Nickdev8/LedScreen/daftpunkfiles/gloves/images/2013-06-19_19.33.11.jpg

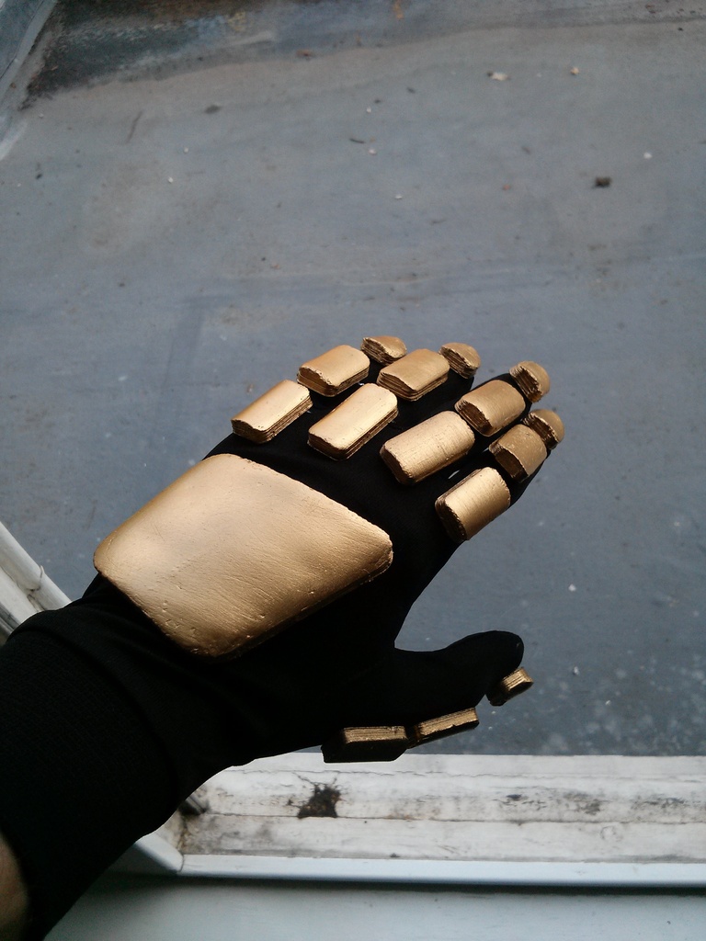
daftpunkfiles/gloves/images/2013-06-19_19.33.11.jpg
