Nickdev8/LedScreen/daftpunkfiles/thomas/p1/images/DisplayLowerBracket-v1.3.jpg

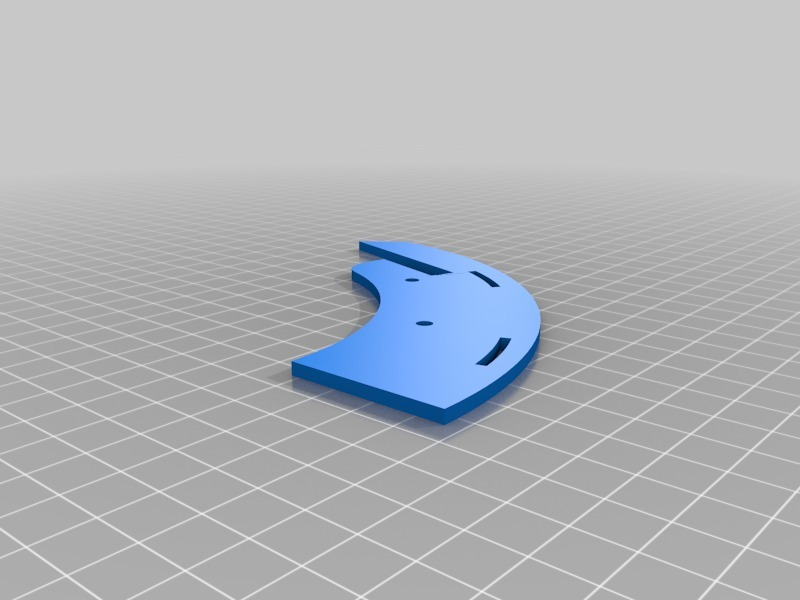
daftpunkfiles/thomas/p1/images/DisplayLowerBracket-v1.3.jpg
