Nickdev8/LedScreen/daftpunkfiles/thomas/p1/images/DisplayupperBracket-v1.3.jpg

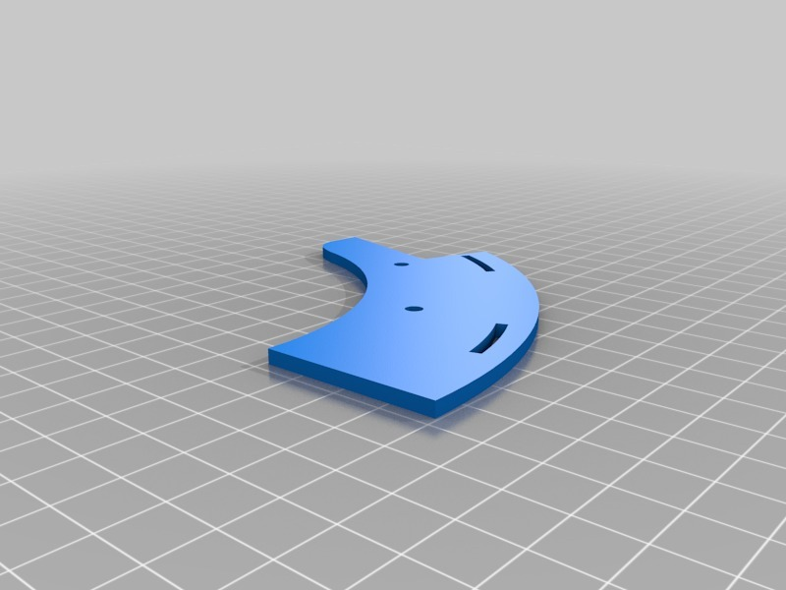
daftpunkfiles/thomas/p1/images/DisplayupperBracket-v1.3.jpg
