Nickdev8/LedScreen/daftpunkfiles/thomas/p1/images/IMG_20140508_220246.jpg

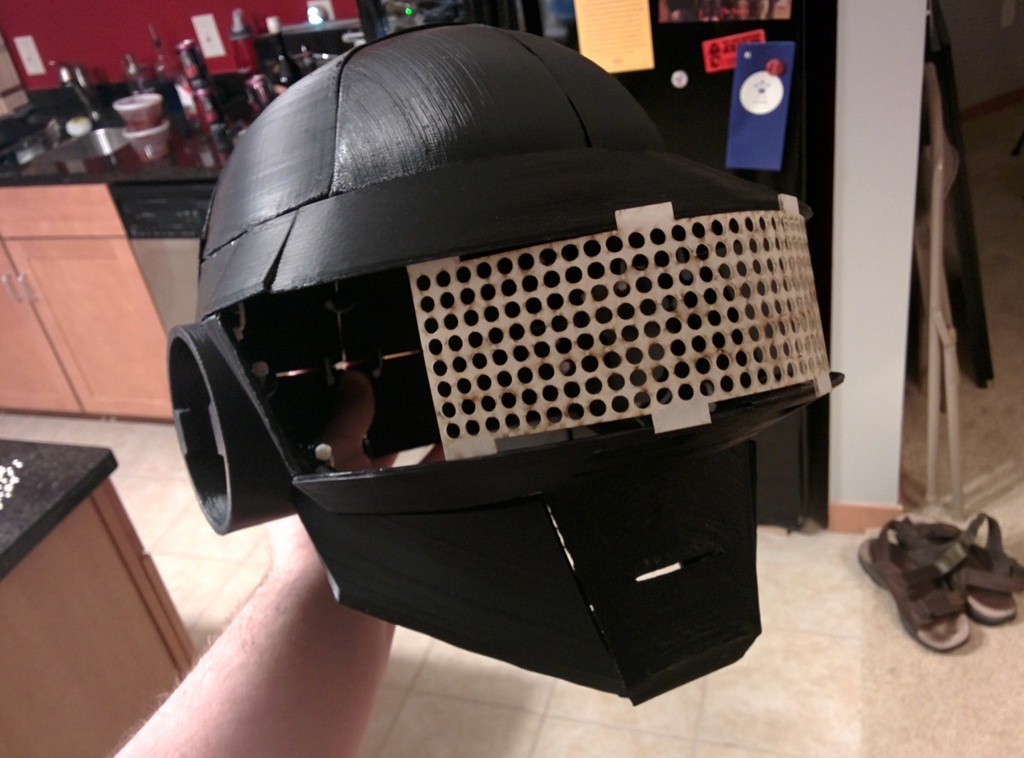
daftpunkfiles/thomas/p1/images/IMG_20140508_220246.jpg
