Nickdev8/LedScreen/daftpunkfiles/thomas/p1/images/June_10__2014_at_1221AM.jpg

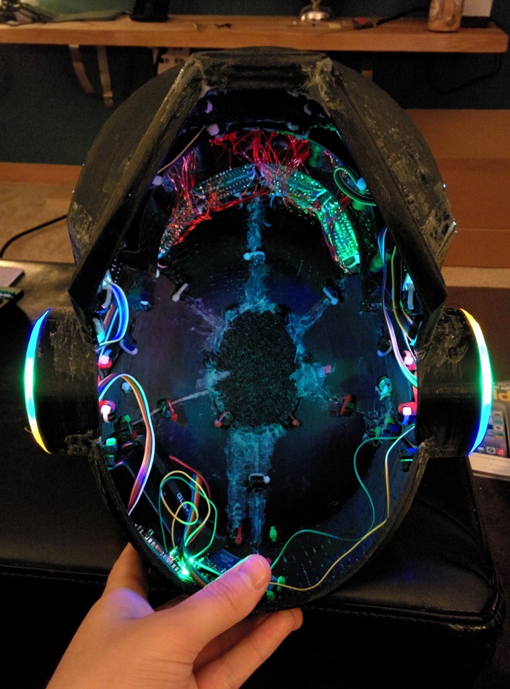
daftpunkfiles/thomas/p1/images/June_10__2014_at_1221AM.jpg
