Nickdev8/LedScreen/daftpunkfiles/thomas/p1/images/LightRing-v1.0.jpg

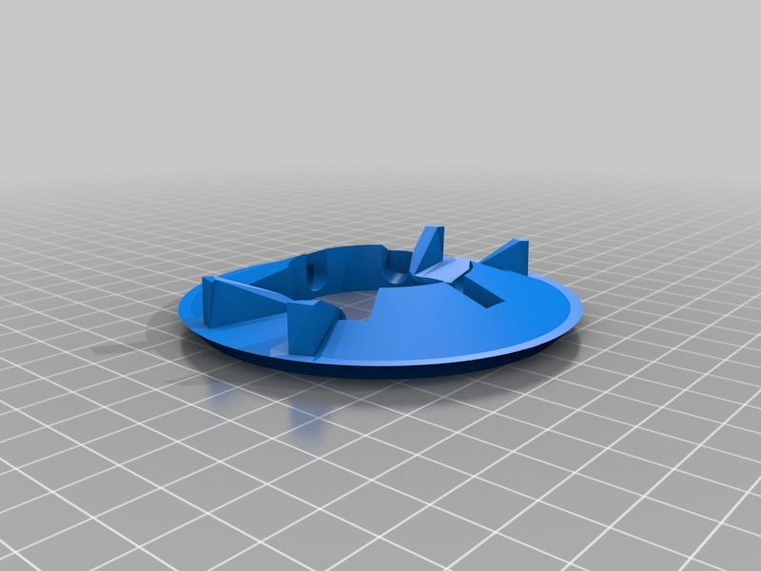
daftpunkfiles/thomas/p1/images/LightRing-v1.0.jpg
