Nickdev8/LedScreen/daftpunkfiles/thomas/p1/images/May_25__2014_at_0116AM.jpg

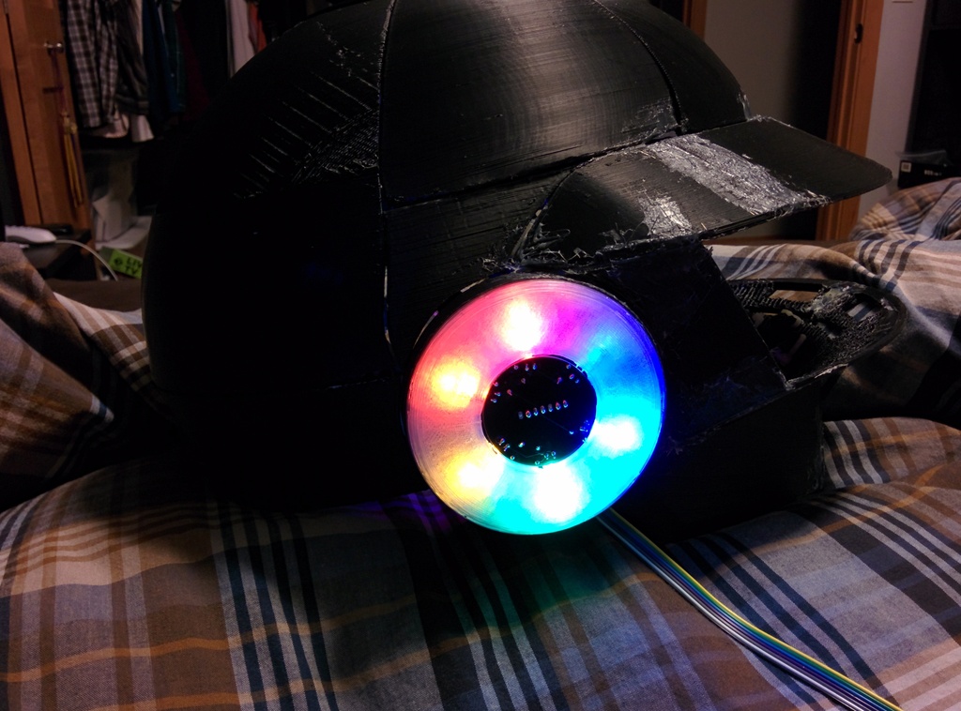
daftpunkfiles/thomas/p1/images/May_25__2014_at_0116AM.jpg
