Nickdev8/LedScreen/daftpunkfiles/thomas/p1/images/November_02__2014_at_0414PM.jpeg

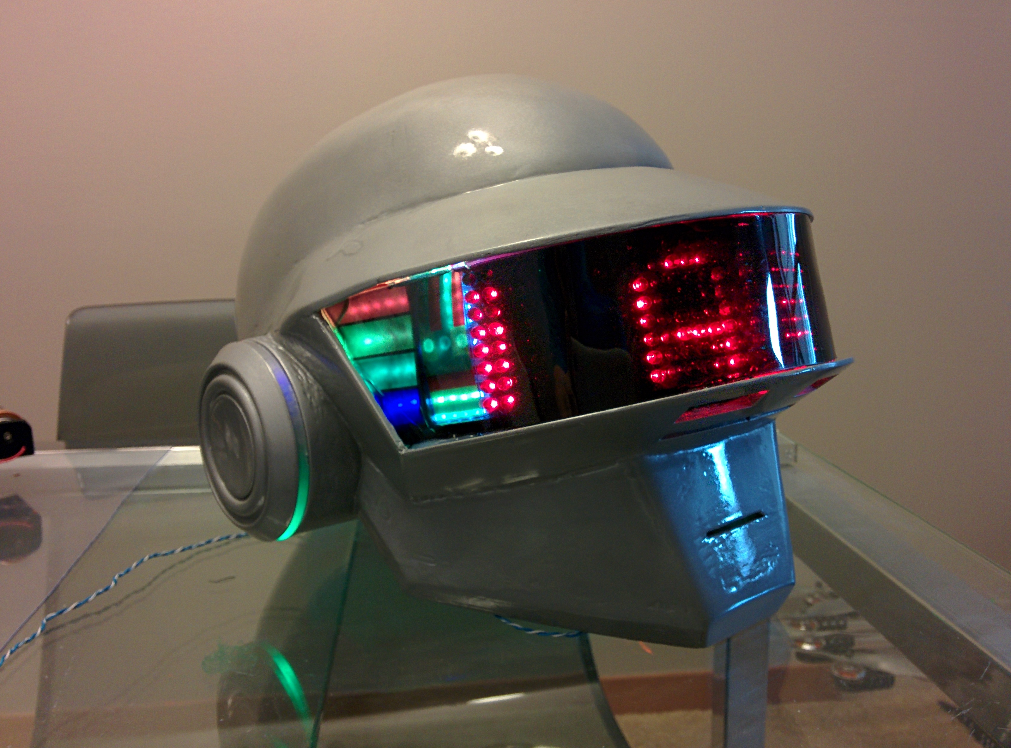
daftpunkfiles/thomas/p1/images/November_02__2014_at_0414PM.jpeg
