Nickdev8/LedScreen/daftpunkfiles/thomas/p1/images/Thomas_Helmet-BottomVisor-Front.jpg

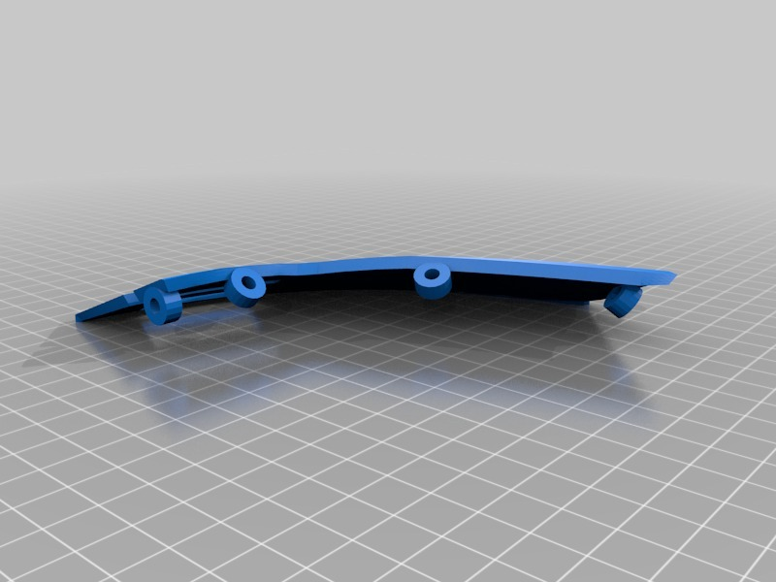
daftpunkfiles/thomas/p1/images/Thomas_Helmet-BottomVisor-Front.jpg
