Nickdev8/LedScreen/daftpunkfiles/thomas/p1/images/Thomas_Helmet-Cheek.jpg

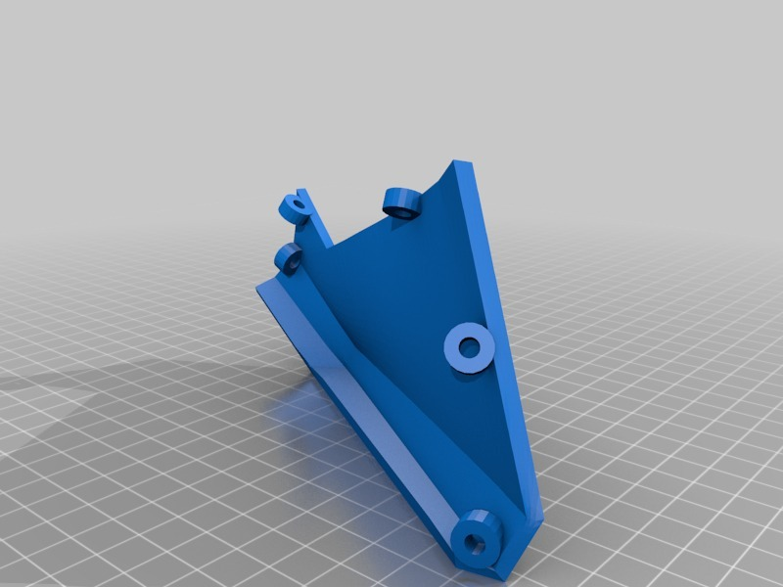
daftpunkfiles/thomas/p1/images/Thomas_Helmet-Cheek.jpg
