Nickdev8/LedScreen/daftpunkfiles/thomas/p1/images/Thomas_Helmet-Dome-Back-Bottom.jpg

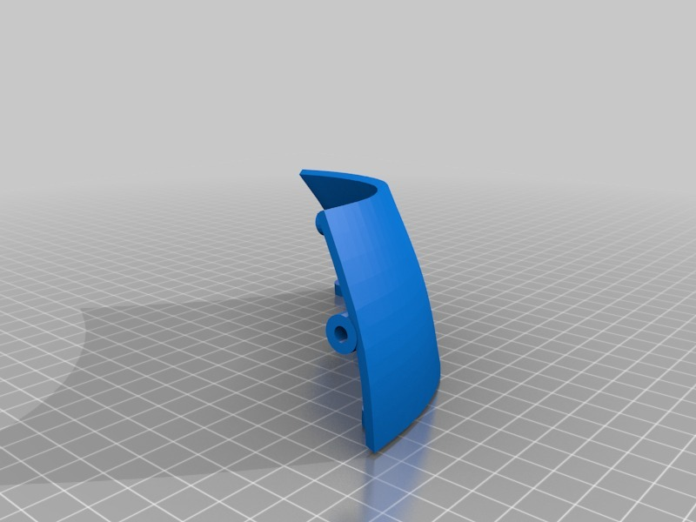
daftpunkfiles/thomas/p1/images/Thomas_Helmet-Dome-Back-Bottom.jpg
