Nickdev8/LedScreen/daftpunkfiles/thomas/p1/images/Thomas_Helmet-Dome-Back-Top.jpg

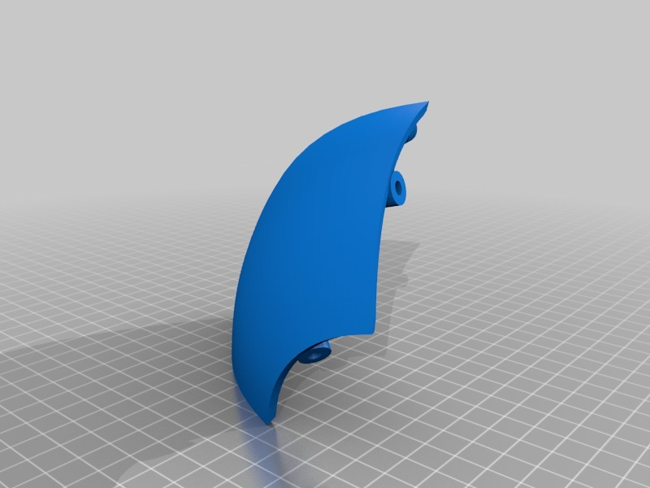
daftpunkfiles/thomas/p1/images/Thomas_Helmet-Dome-Back-Top.jpg
