Nickdev8/LedScreen/daftpunkfiles/thomas/p1/images/Thomas_Helmet-Dome-Front.jpg

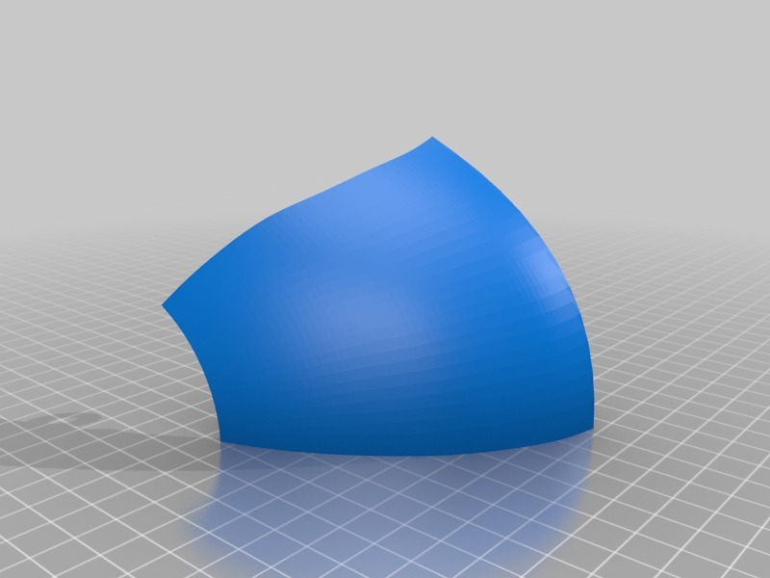
daftpunkfiles/thomas/p1/images/Thomas_Helmet-Dome-Front.jpg
