Nickdev8/LedScreen/daftpunkfiles/thomas/p1/images/Thomas_Helmet-Dome-SideTip-V1.5.jpg

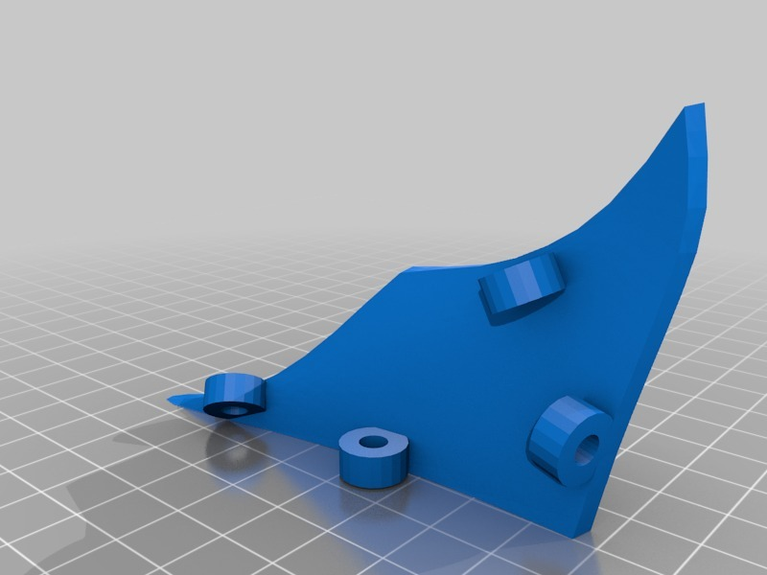
daftpunkfiles/thomas/p1/images/Thomas_Helmet-Dome-SideTip-V1.5.jpg
