Nickdev8/LedScreen/daftpunkfiles/thomas/p1/images/Thomas_Helmet-EarCap.jpg

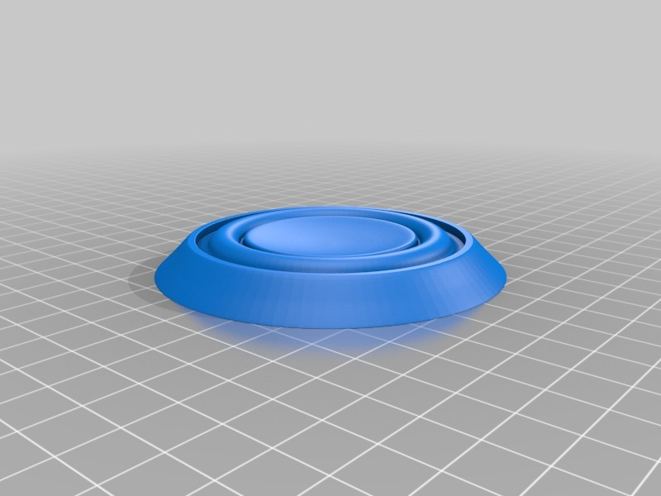
daftpunkfiles/thomas/p1/images/Thomas_Helmet-EarCap.jpg
