Nickdev8/LedScreen/daftpunkfiles/thomas/p1/images/Thomas_Helmet-EarMount-v1.0.jpg

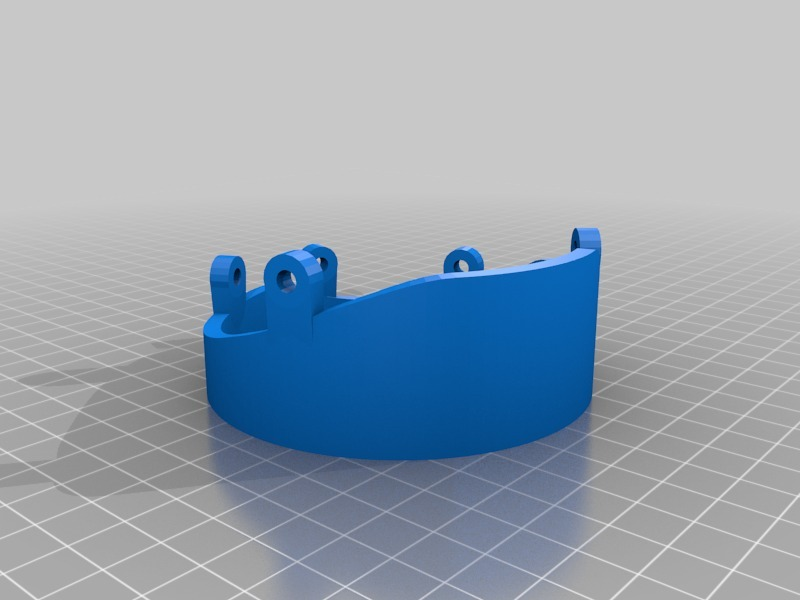
daftpunkfiles/thomas/p1/images/Thomas_Helmet-EarMount-v1.0.jpg
