Nickdev8/LedScreen/daftpunkfiles/thomas/p1/images/Thomas_Helmet-TopVisor-Side.jpg

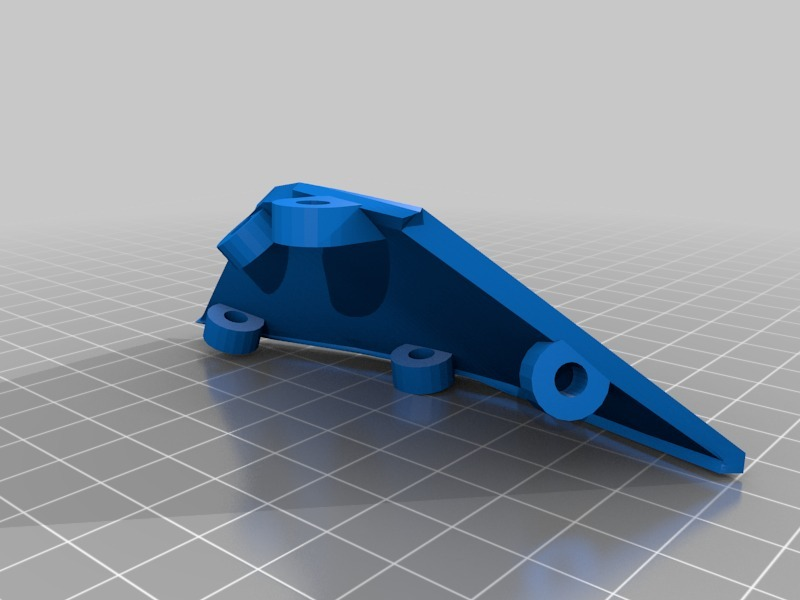
daftpunkfiles/thomas/p1/images/Thomas_Helmet-TopVisor-Side.jpg
