Nickdev8/LedScreen/daftpunkfiles/thomas/p1/images/Thomas_Helmet-Visor-TopFront.jpg

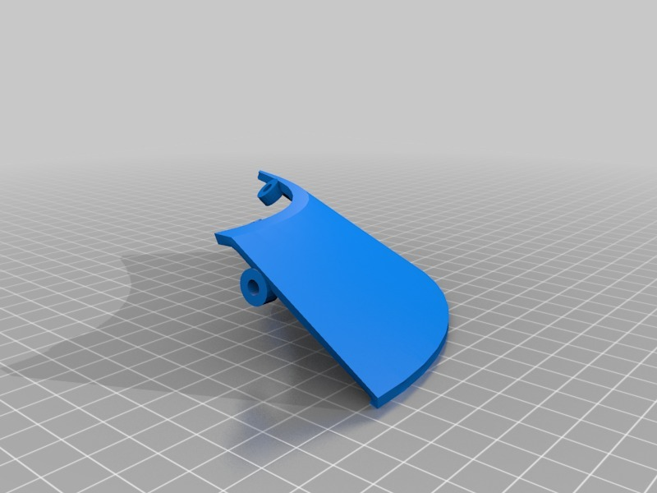
daftpunkfiles/thomas/p1/images/Thomas_Helmet-Visor-TopFront.jpg
