Nickdev8/LedScreen/docs/images/aliexpresscart.png

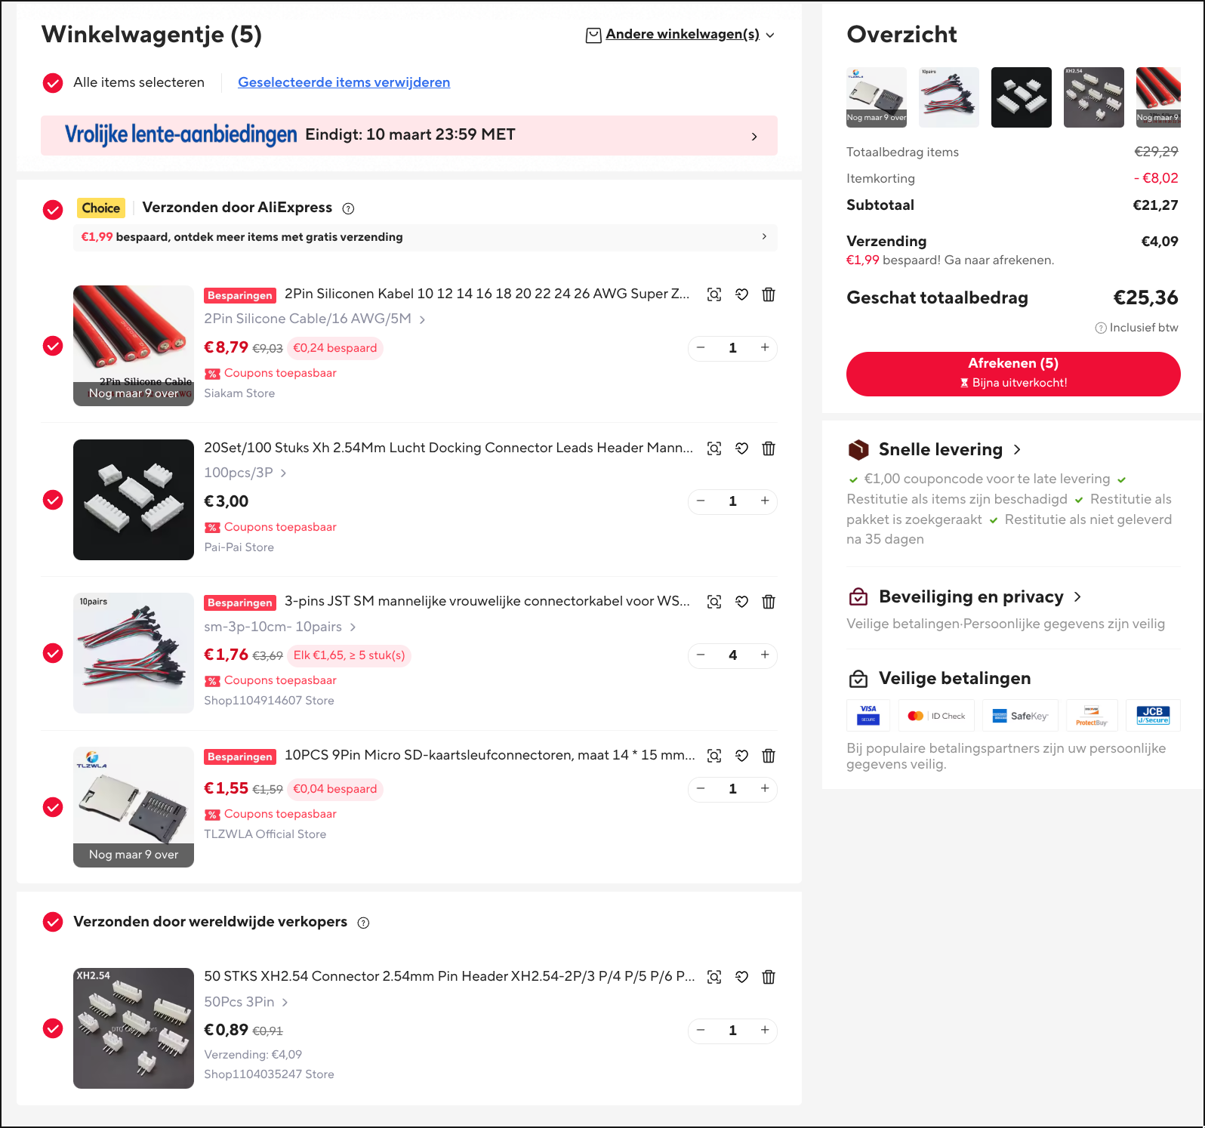
docs/images/aliexpresscart.png
