Nickdev8/LedScreen/docs/images/amazoncart.png

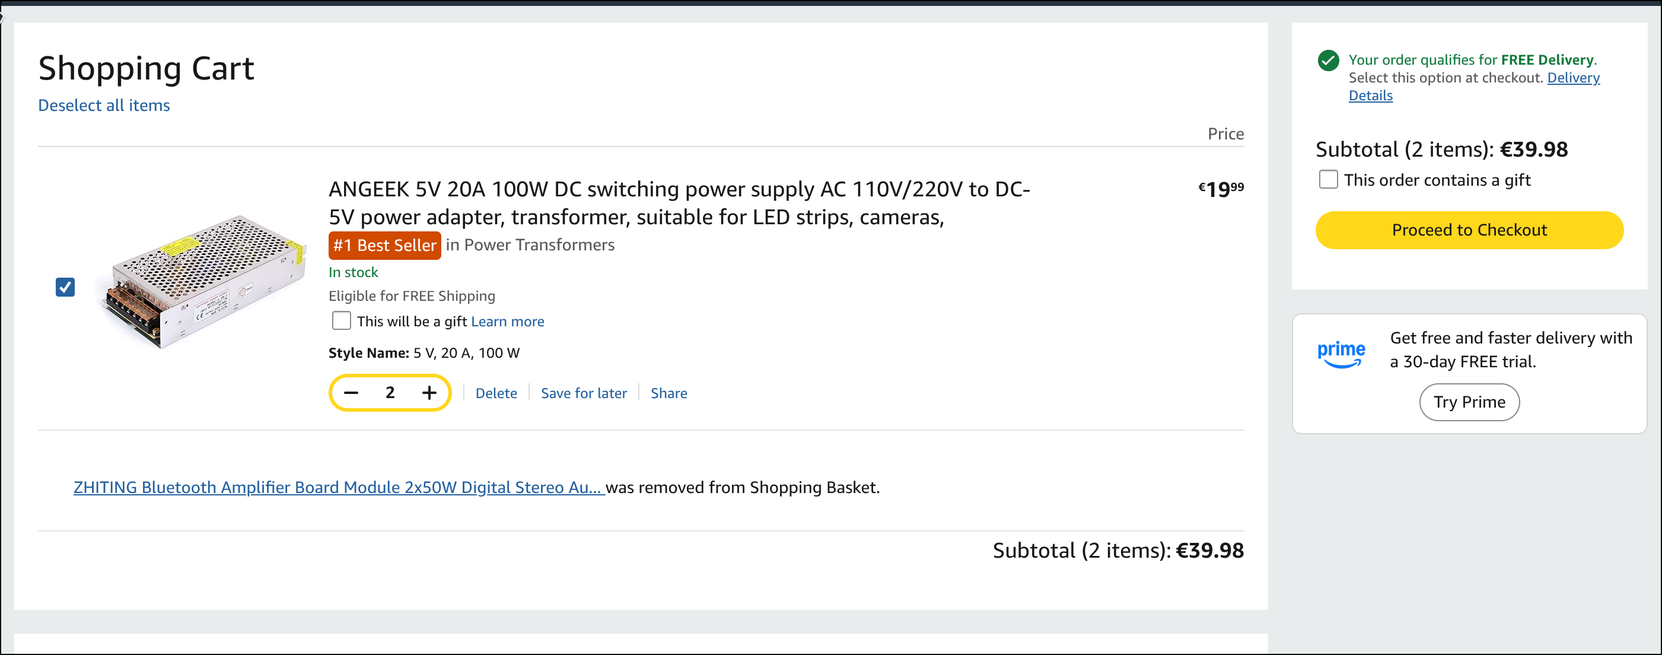
docs/images/amazoncart.png
