Nickdev8/LedScreen/docs/images/jlcpcbcart2.png

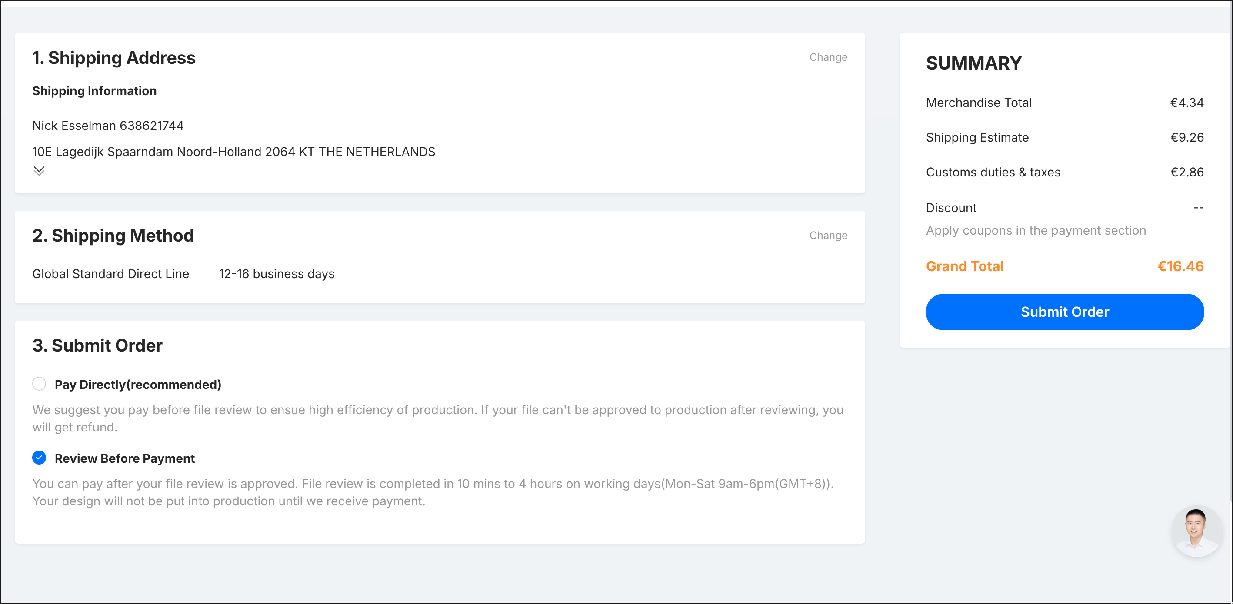
docs/images/jlcpcbcart2.png
