Nickdev8/LedScreen/docs/images/jlcpcbcart.png

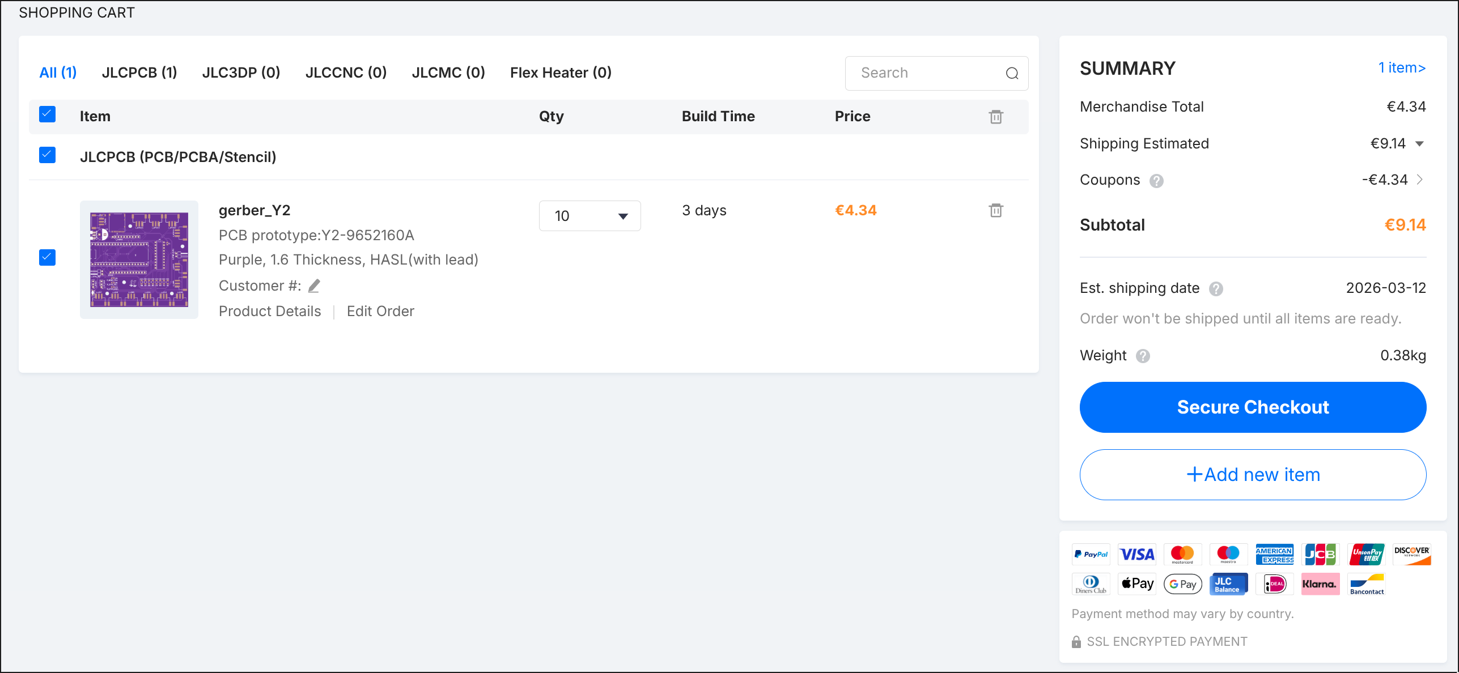
docs/images/jlcpcbcart.png
