Nickdev8/LedScreen/docs/images/kiwielectonicscart.png

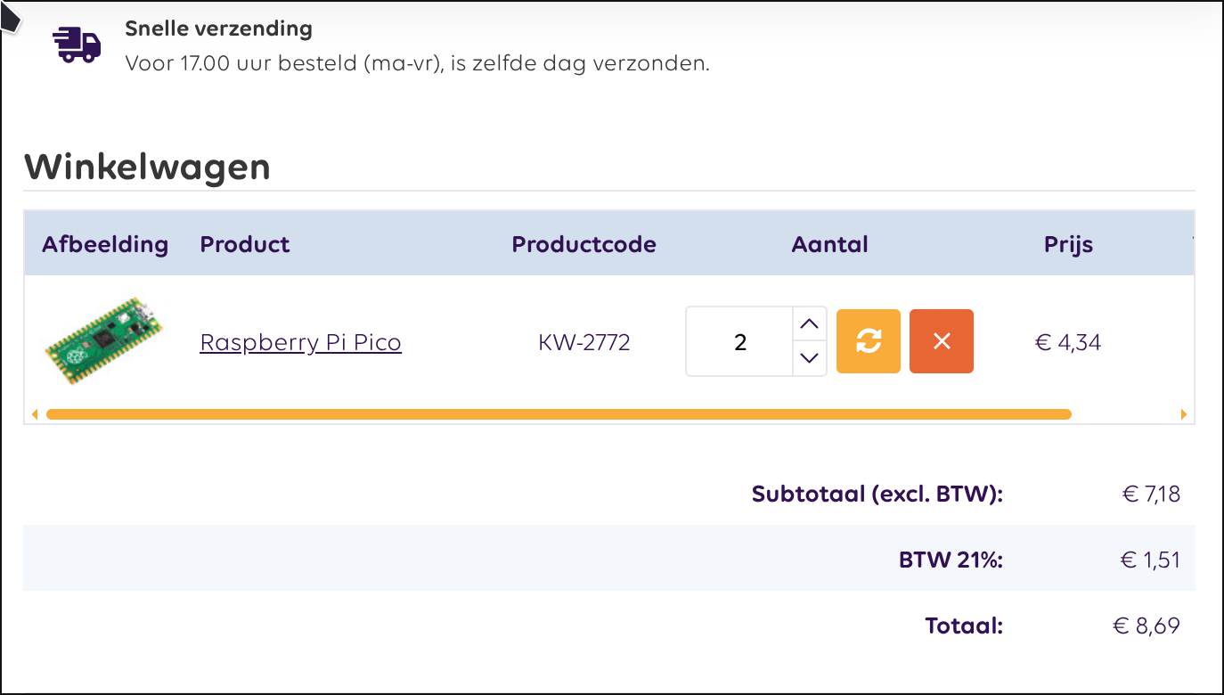
docs/images/kiwielectonicscart.png
