Nickdev8/LedScreen/docs/images/lcsccart.png

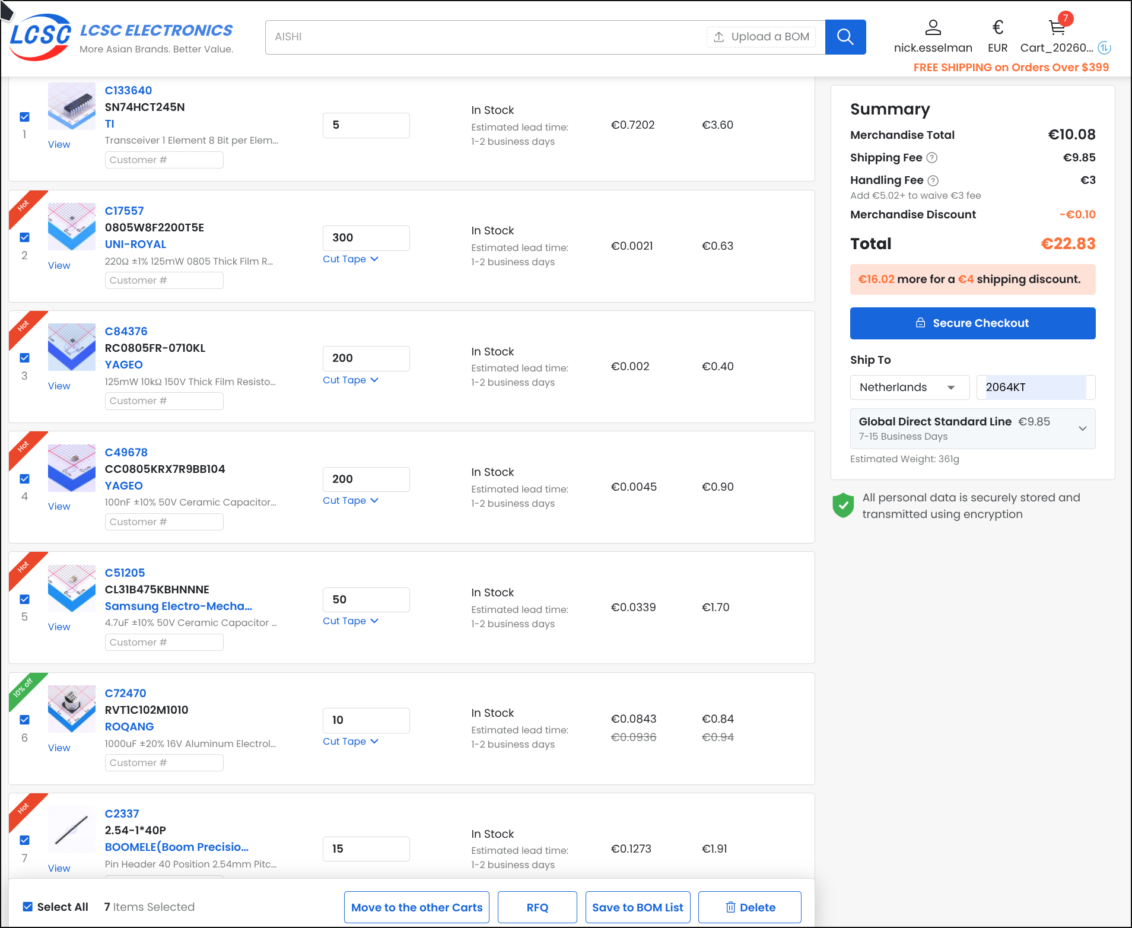
docs/images/lcsccart.png
