Nickdev8/LedScreen/pcb/src/BoardSize.png

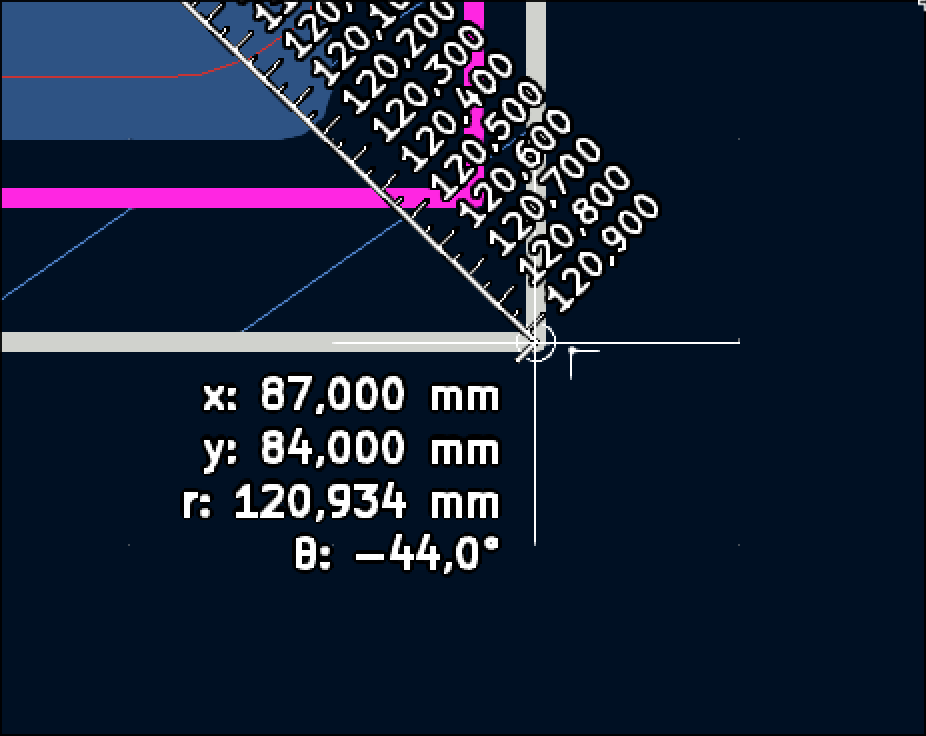
pcb/src/BoardSize.png
