Nickdev8/LedScreen/xlights_project/house.png

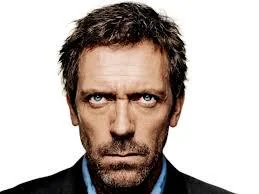
xlights_project/house.png
