Nickdev8/LedScreen/daftpunkfiles/guy manual/visor4.stl

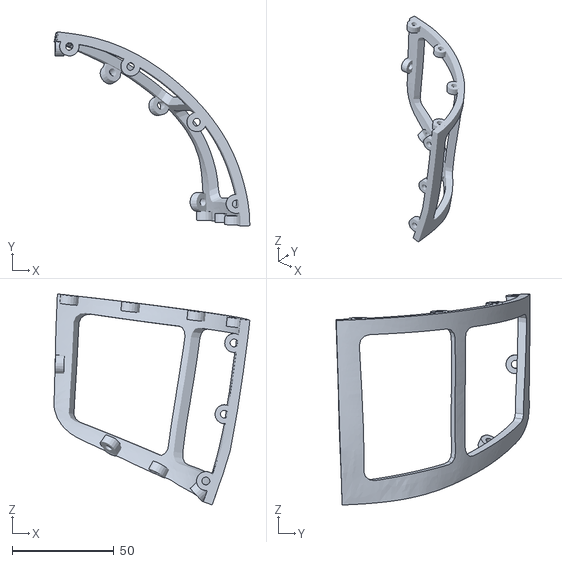
[picture p62: CAD file, 2026-06-18]
daftpunkfiles/guy manual/visor4.stl
96.2 x 95.4 x 103.6
