Nickdev8/LedScreen/daftpunkfiles/thomas/p1/files/Thomas_Helmet-Dome-Side.stl

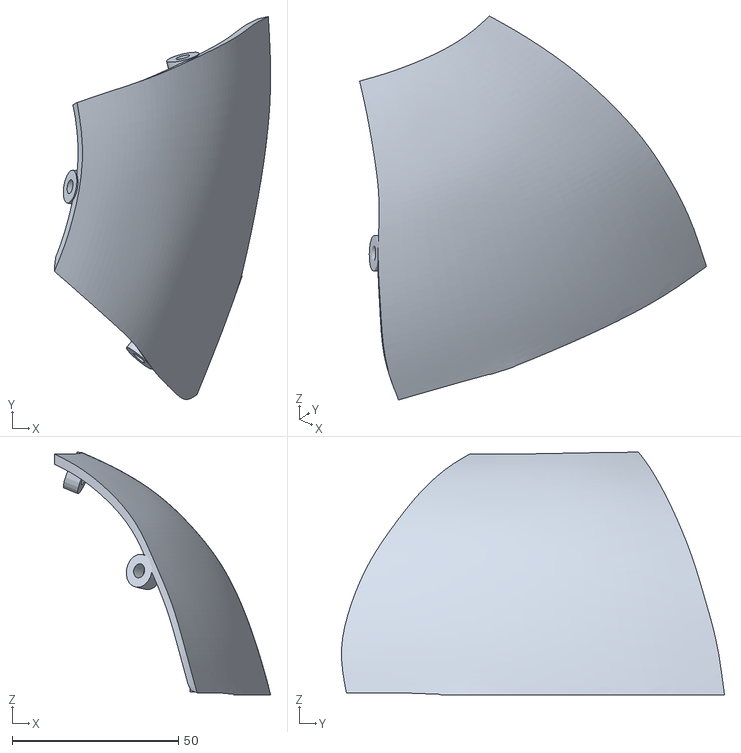
[picture p63: CAD file, 2026-06-18]
daftpunkfiles/thomas/p1/files/Thomas_Helmet-Dome-Side.stl
65.1 x 115.3 x 73.0
