Nickdev8/LedScreen/daftpunkfiles/thomas/p2/files/Thomas_Helmet-Mouth-V1.5.stl

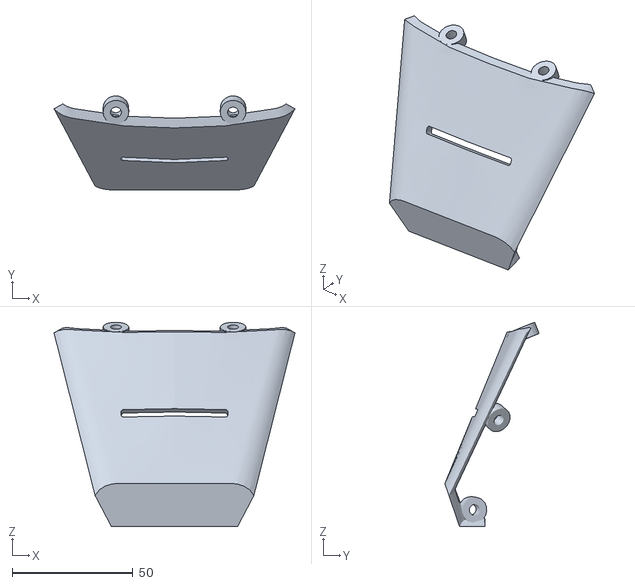
[picture p64: CAD file, 2026-06-18]
daftpunkfiles/thomas/p2/files/Thomas_Helmet-Mouth-V1.5.stl
99.9 x 39.1 x 84.8
