Nickdev8/LedScreen/daftpunkfiles/thomas/thomas-1side.3mf

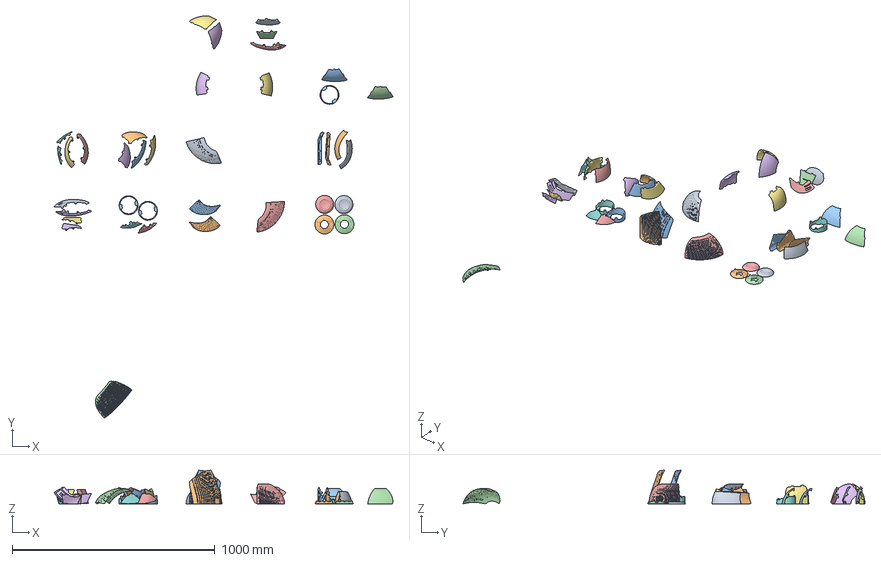
[picture p65: CAD file, 2026-06-18]
daftpunkfiles/thomas/thomas-1side.3mf
1670.5 x 1982.1 x 165.4 mm
Thomas_Helmet-BottomVisor-Front-V1.5.stl x 2
Thomas_Helmet-Cheek-V1.5.stl
Thomas_Helmet-EarMount-v1.5.stl x 2
Thomas_Helmet-Mouth-V1.5.stl
Thomas_Helmet-TopVisor-Side-V1.5.stl
Thomas_Helmet-Visor-Side-V1.5.stl
Thomas_Helmet-Dome-Back-Mid-V1.5.stl
Thomas_Helmet-Dome-SideTip-V1.5.stl
Thomas_Helmet-Dome-Top-V1.5.stl
Thomas_Helmet-Dome-Front-V1.5.stl
Thomas_Helmet-Visor-TopFront-V1.5.stl
LightRing-v1.5.stl
Thomas_Helmet-EarCap-V1.5.stl
M-Thomas_Helmet-BottomVisor-Front-V1.5.stl
M-Thomas_Helmet-Visor-Side-V1.5.stl
M-Thomas_Helmet-TopVisor-Side-V1.5.stl
M-Thomas_Helmet-EarCap-V1.5.stl
M-LightRing-v1.5.stl
M-Thomas_Helmet-Cheek-V1.5.stl
M-Thomas_Helmet-Dome-SideTip-V1.5.stl
M-Thomas_Helmet-Dome-Back-Mid-V1.5.stl
M-Thomas_Helmet-Dome-Front-V1.5.stl
M-Thomas_Helmet-Visor-TopFront-V1.5.stl
M-Thomas_Helmet-EarMount-v1.5.stl
Thomas_Helmet-Dome-Back-Bottom-v1.5.stl
M-Thomas_Helmet-Dome-Back-Bottom-v1.5.stl
Thomas_Helmet-Dome-Side-V1.5.stl
M-Thomas_Helmet-Dome-Side-V1.5.stl
Thomas_Helmet-Dome-Back-Top-V1.5.stl
M-Thomas_Helmet-Dome-Back-Top-V1.5.stl
M-visor1.stl
visor2.stl
M-visor2.stl
visor1.stl x 2
BackWireHarness-V1.5.stl
M-BackWireHarness-V1.5.stl
