Nickdev8/LedScreen/daftpunkfiles/visorwithholes.stl

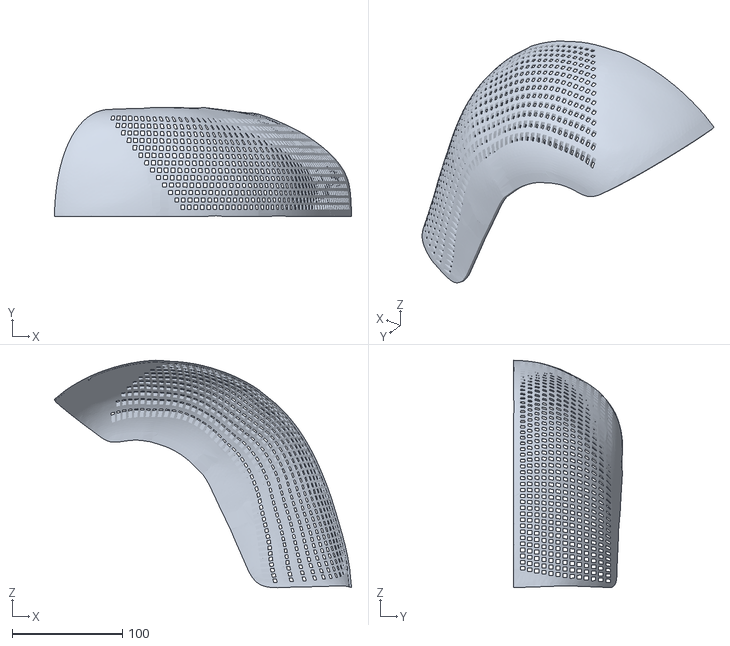
[picture p66: CAD file, 2026-06-18]
daftpunkfiles/visorwithholes.stl
269.1 x 98.7 x 206.1
