Nickdev8/LedScreen/daftpunkfiles/gloves/files/Pinky.stl

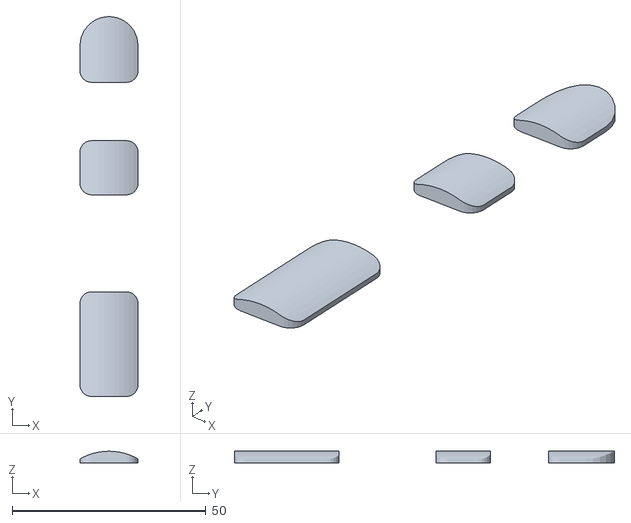
[picture p67: CAD file, 2026-06-18]
daftpunkfiles/gloves/files/Pinky.stl
15.0 x 98.0 x 3.00
