Nickdev8/LedScreen/daftpunkfiles/guy manual/files/VisorSideVacSupportBack-v1.5.stl

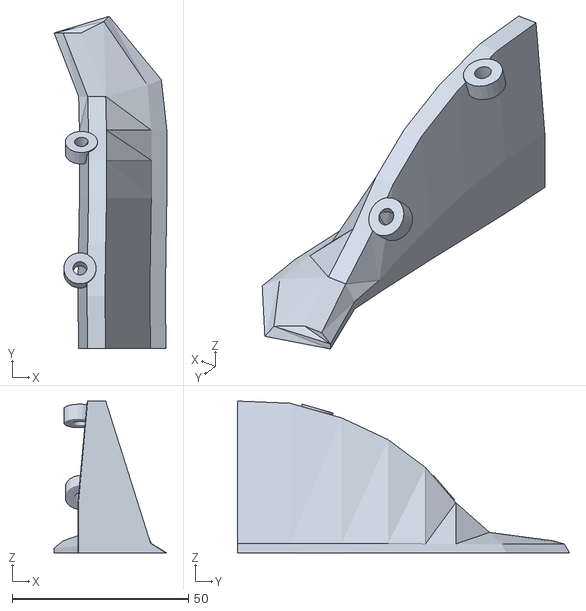
[picture p68: CAD file, 2026-06-18]
daftpunkfiles/guy manual/files/VisorSideVacSupportBack-v1.5.stl
32.0 x 94.3 x 43.1
