Nickdev8/LedScreen/daftpunkfiles/guy manual/visor1.stl

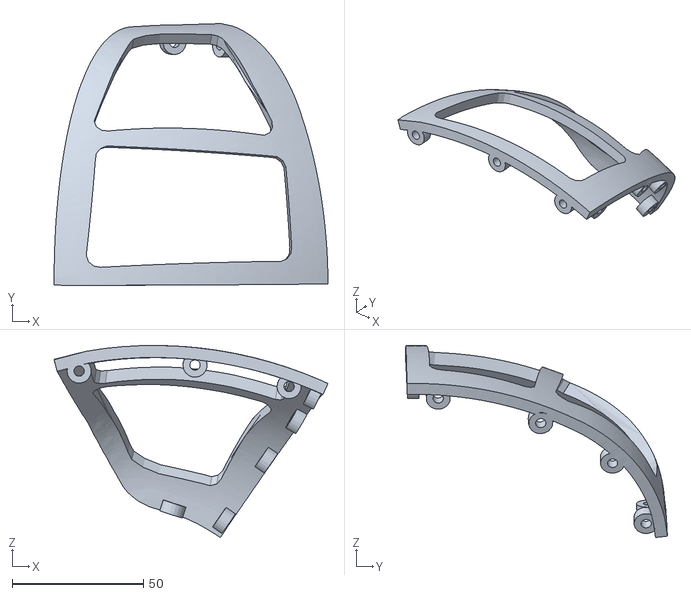
[picture p69: CAD file, 2026-06-18]
daftpunkfiles/guy manual/visor1.stl
104.4 x 99.8 x 73.2
