Nickdev8/LedScreen/daftpunkfiles/thomas/p1/files/Thomas_Helmet-Dome-Back-Bottom-v1.5.stl

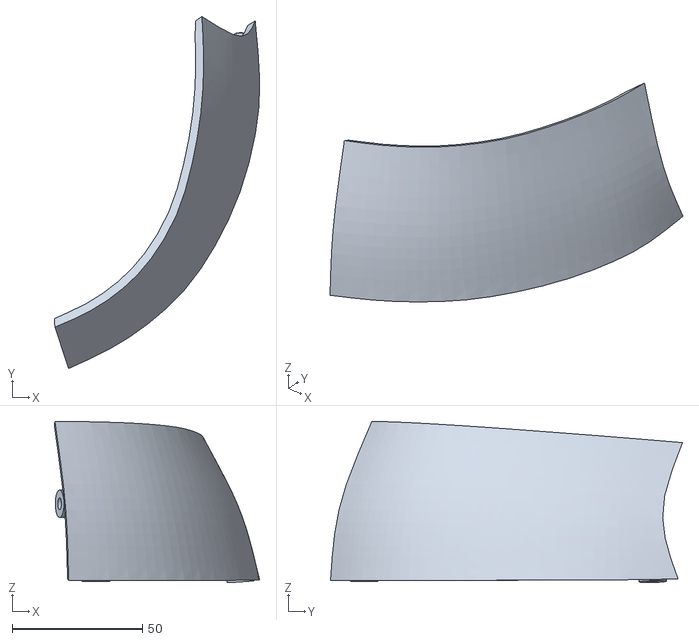
[picture p70: CAD file, 2026-06-18]
daftpunkfiles/thomas/p1/files/Thomas_Helmet-Dome-Back-Bottom-v1.5.stl
79.0 x 135.3 x 62.0
