Nickdev8/LedScreen/daftpunkfiles/thomas/p2/files/Thomas_Helmet-Dome-Front-V1.5.stl

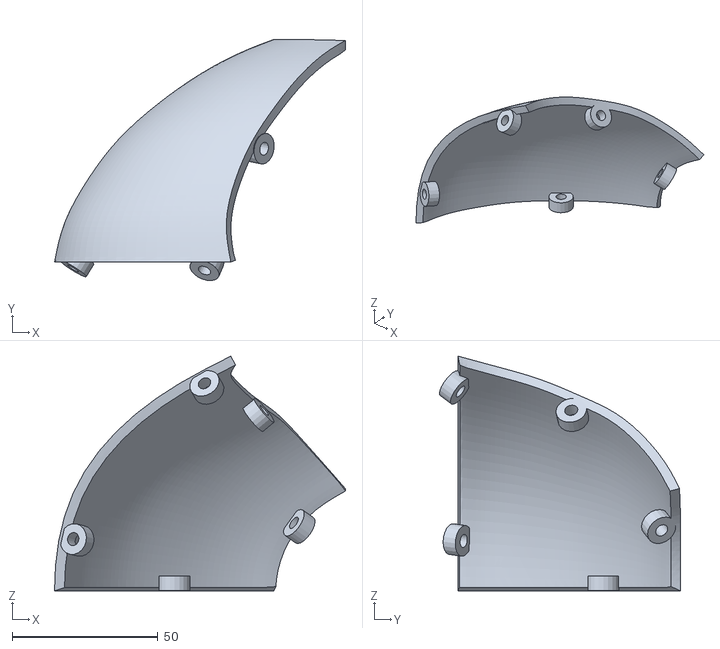
[picture p71: CAD file, 2026-06-18]
daftpunkfiles/thomas/p2/files/Thomas_Helmet-Dome-Front-V1.5.stl
99.9 x 82.8 x 80.6
