Nickdev8/LedScreen/daftpunkfiles/thomasvisorl.stl

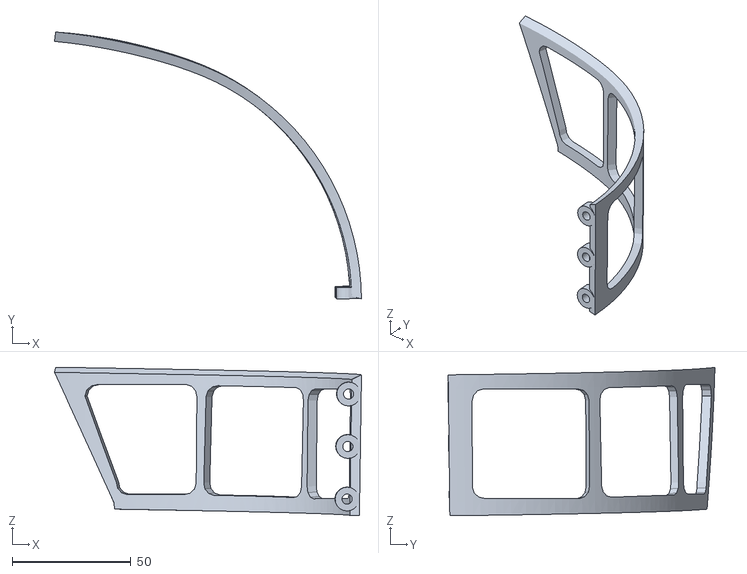
[picture p72: CAD file, 2026-06-18]
daftpunkfiles/thomasvisorl.stl
129.4 x 112.5 x 62.6
