Nickdev8/LedScreen/daftpunkfiles/guy manual/files/BackWireHarness-V1.5.stl

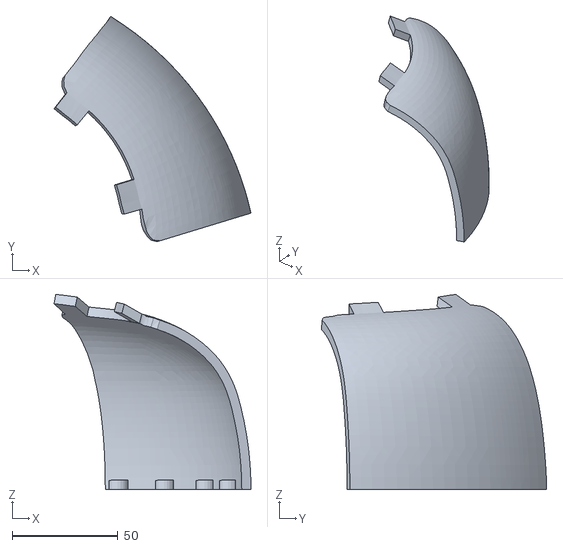
[picture p73: CAD file, 2026-06-18]
daftpunkfiles/guy manual/files/BackWireHarness-V1.5.stl
93.3 x 106.7 x 92.4
