Nickdev8/LedScreen/daftpunkfiles/guy manual/visor2.stl

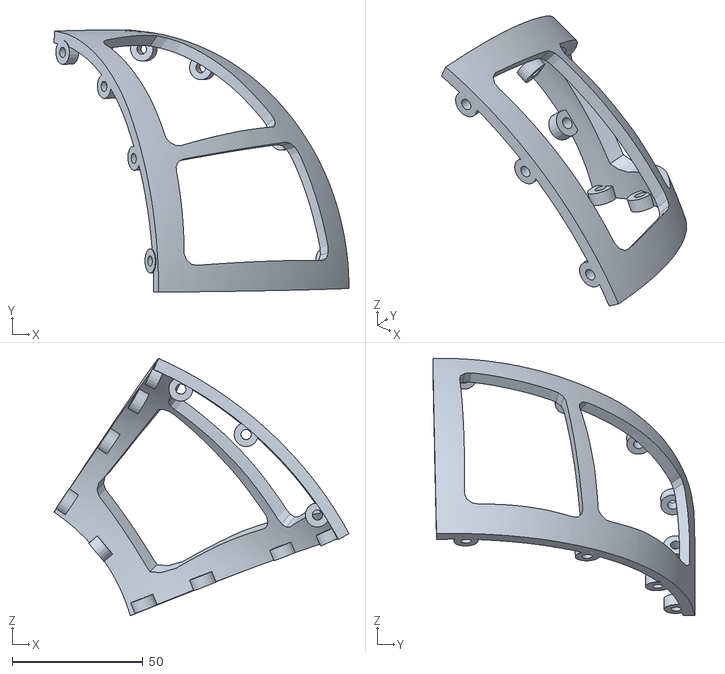
[picture p74: CAD file, 2026-06-18]
daftpunkfiles/guy manual/visor2.stl
112.6 x 100.1 x 98.2
