Nickdev8/LedScreen/daftpunkfiles/thomas/p1/files/Thomas_Helmet-Dome-Back-Mid-V1.5.stl

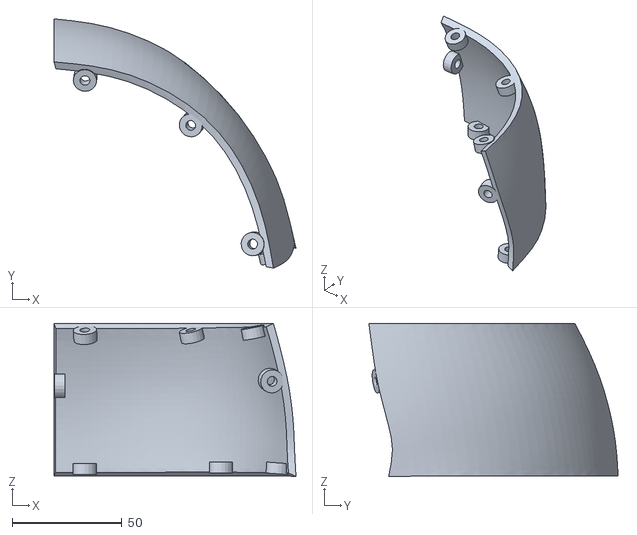
[picture p75: CAD file, 2026-06-18]
daftpunkfiles/thomas/p1/files/Thomas_Helmet-Dome-Back-Mid-V1.5.stl
110.1 x 113.4 x 69.7
