Nickdev8/LedScreen/daftpunkfiles/thomas/p2/files/Thomas_Helmet-EarCap-V1.5.stl

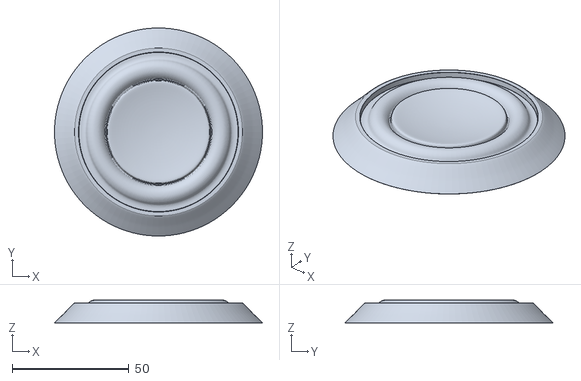
[picture p76: CAD file, 2026-06-18]
daftpunkfiles/thomas/p2/files/Thomas_Helmet-EarCap-V1.5.stl
88.9 x 88.9 x 9.77
