Nickdev8/LedScreen/daftpunkfiles/visorwithholes2.stl

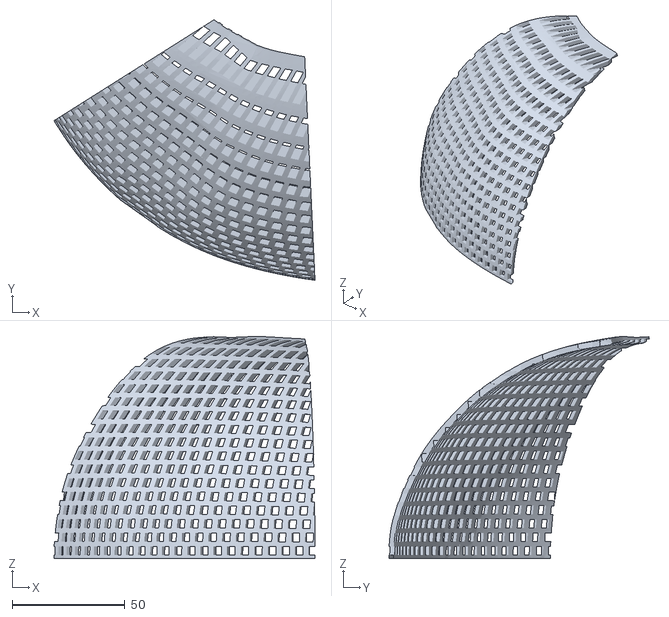
[picture p77: CAD file, 2026-06-18]
daftpunkfiles/visorwithholes2.stl
115.6 x 115.4 x 98.5
