Nickdev8/LedScreen/daftpunkfiles/guy manual/files/VisorMidTop-v1.5.stl

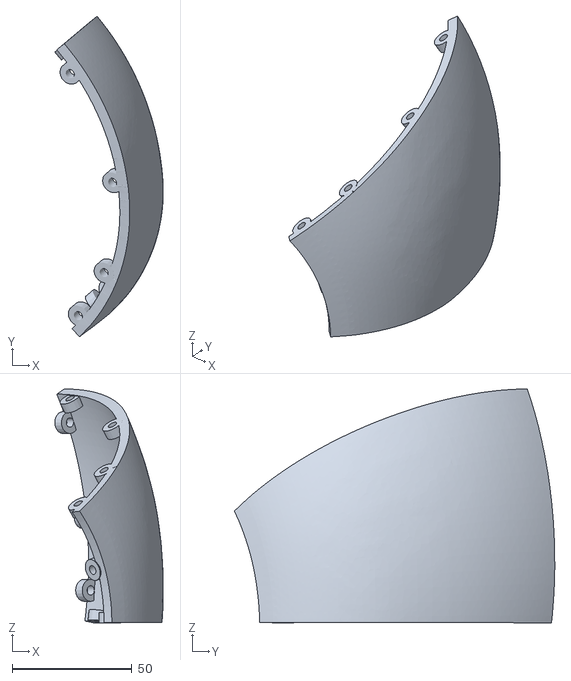
[picture p78: CAD file, 2026-06-18]
daftpunkfiles/guy manual/files/VisorMidTop-v1.5.stl
45.2 x 133.7 x 97.6
