Nickdev8/LedScreen/daftpunkfiles/thomas/p1/files/Thomas_Helmet-Dome-Back-Bottom.stl

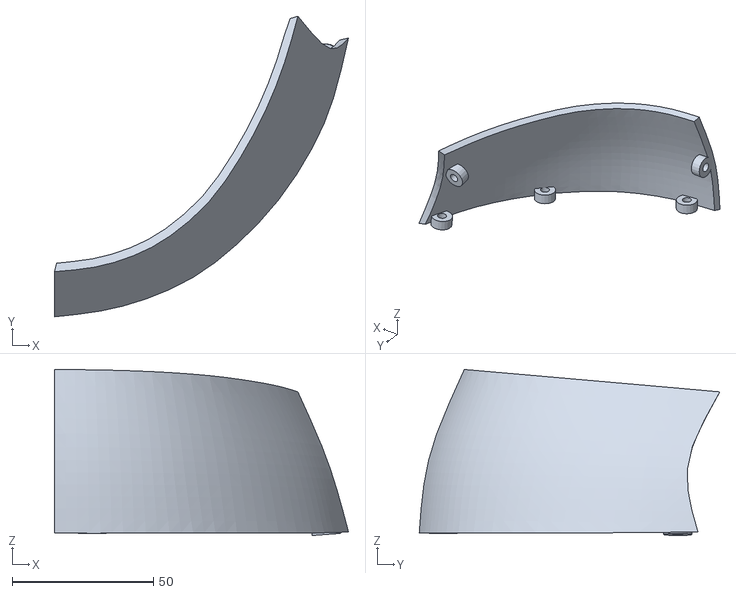
[picture p79: CAD file, 2026-06-18]
daftpunkfiles/thomas/p1/files/Thomas_Helmet-Dome-Back-Bottom.stl
104.0 x 106.4 x 58.8
