Nickdev8/LedScreen/daftpunkfiles/thomas/p2/files/Thomas_Helmet-Dome-Top-V1.5.stl

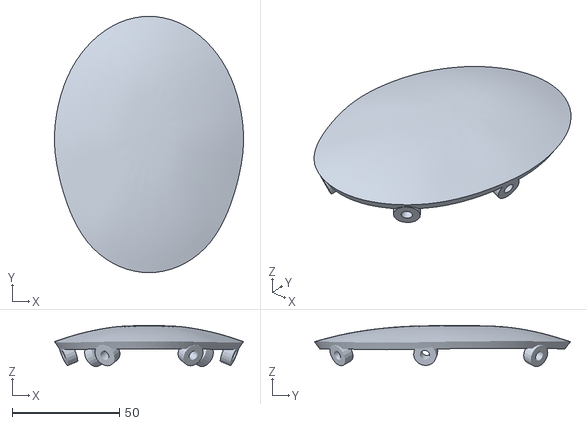
[picture p80: CAD file, 2026-06-18]
daftpunkfiles/thomas/p2/files/Thomas_Helmet-Dome-Top-V1.5.stl
88.1 x 119.5 x 19.3
