Nickdev8/LedScreen/daftpunkfiles/visorwithholes1.stl

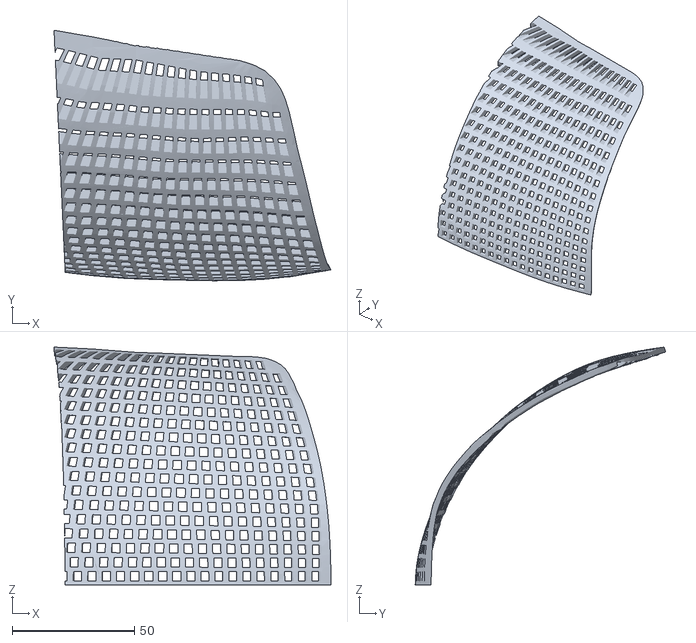
[picture p81: CAD file, 2026-06-18]
daftpunkfiles/visorwithholes1.stl
113.3 x 102.5 x 97.3
