Nickdev8/LedScreen/daftpunkfiles/gloves/files/Thumb.stl

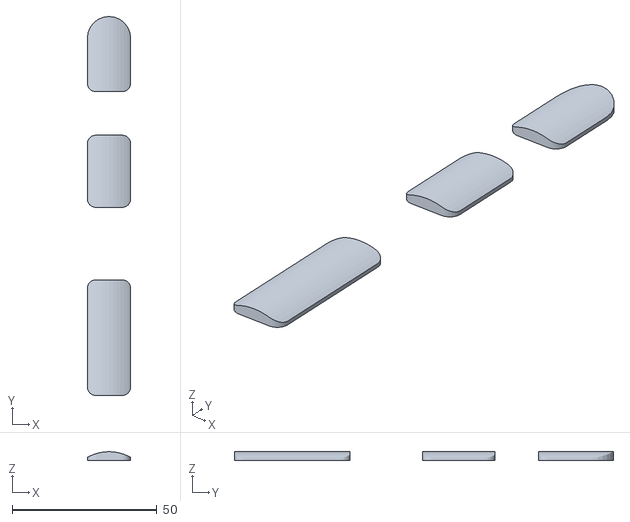
[picture p82: CAD file, 2026-06-18]
daftpunkfiles/gloves/files/Thumb.stl
15.0 x 131.0 x 3.00
