Nickdev8/LedScreen/daftpunkfiles/guy manual/files/Fan-4L-v1.5.stl

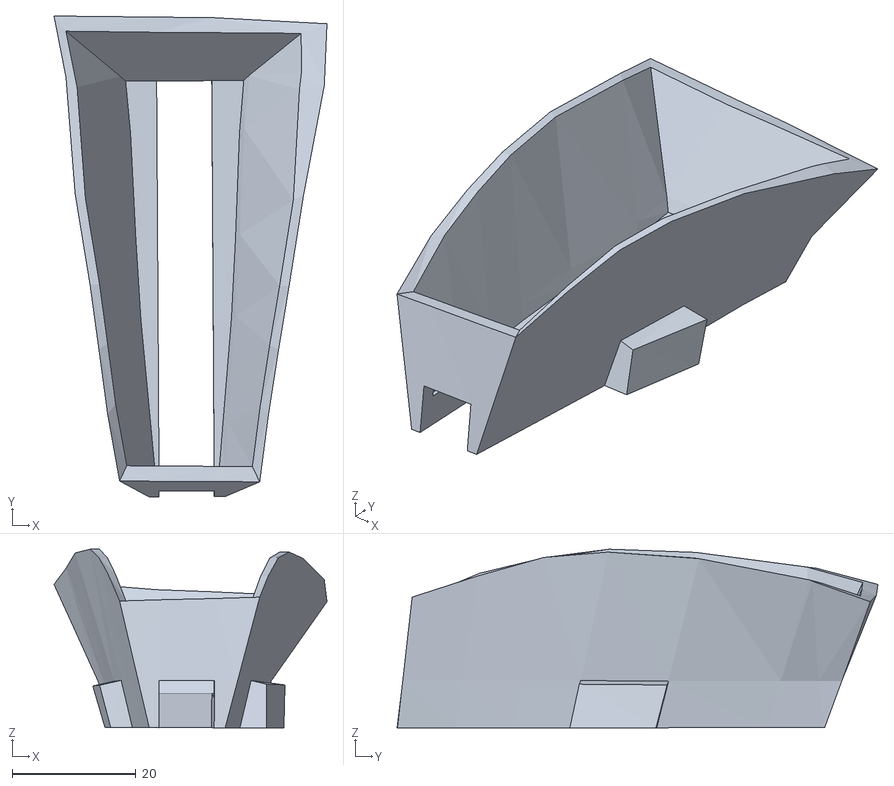
[picture p83: CAD file, 2026-06-18]
daftpunkfiles/guy manual/files/Fan-4L-v1.5.stl
44.2 x 77.9 x 28.9
