Nickdev8/LedScreen/daftpunkfiles/thomas/p1/files/Thomas_Helmet-Visor-Side.stl

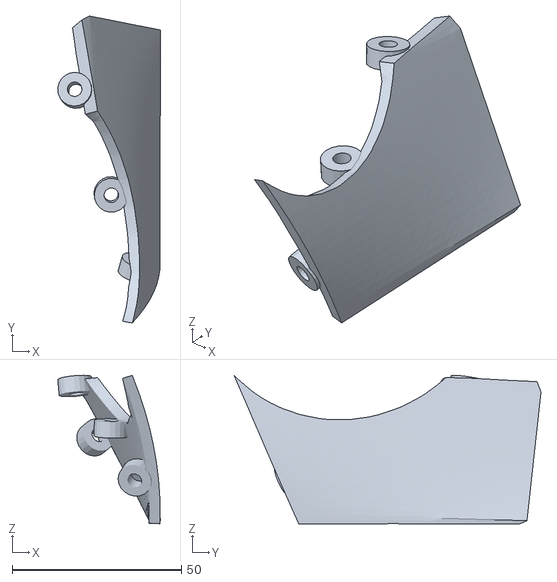
[picture p84: CAD file, 2026-06-18]
daftpunkfiles/thomas/p1/files/Thomas_Helmet-Visor-Side.stl
30.3 x 90.7 x 43.9
