Nickdev8/LedScreen/daftpunkfiles/visor1.stl

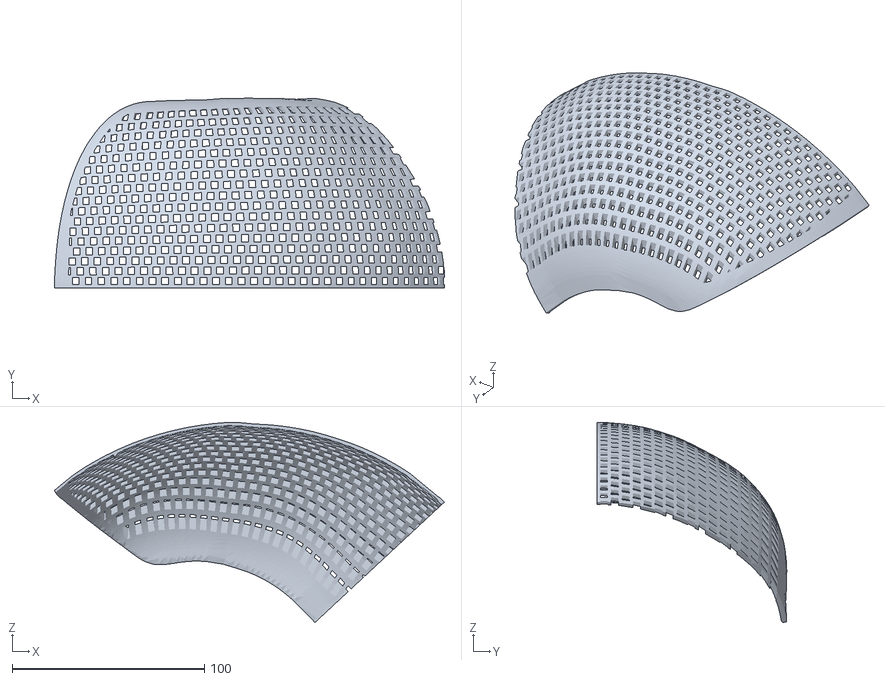
[picture p85: CAD file, 2026-06-18]
daftpunkfiles/visor1.stl
202.8 x 98.5 x 104.2
