Nickdev8/LedScreen/daftpunkfiles/gloves/files/Middle.stl

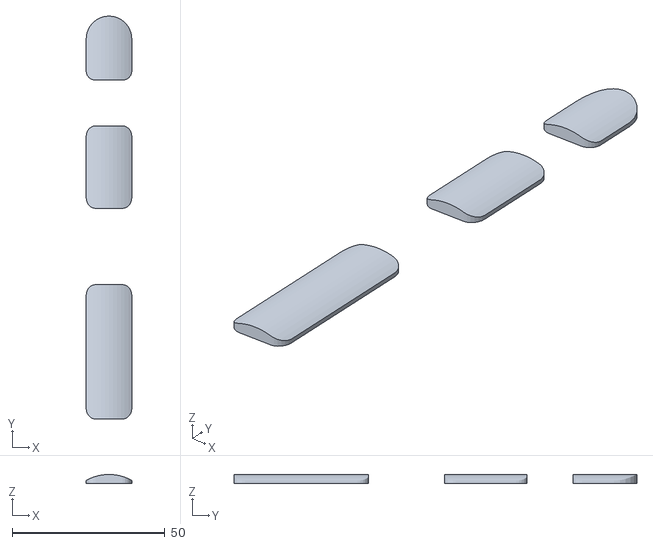
[picture p86: CAD file, 2026-06-18]
daftpunkfiles/gloves/files/Middle.stl
15.0 x 132.0 x 3.00
