Nickdev8/LedScreen/daftpunkfiles/guy manual/files/CircuitPannel-v1.5.stl

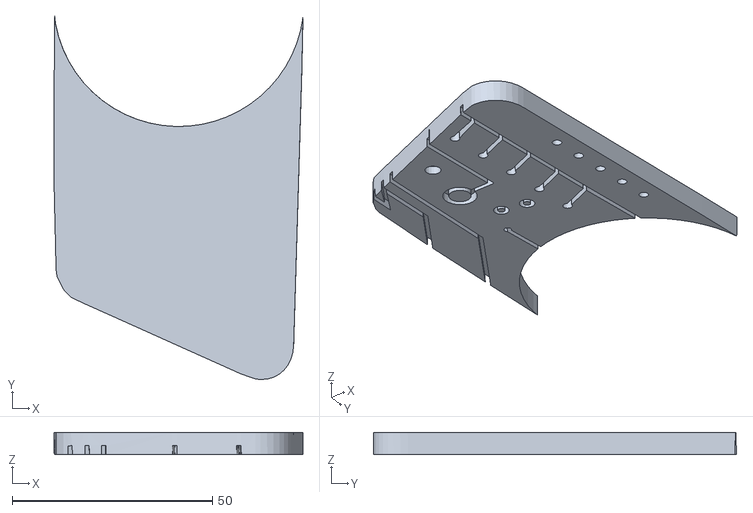
[picture p87: CAD file, 2026-06-18]
daftpunkfiles/guy manual/files/CircuitPannel-v1.5.stl
62.2 x 90.7 x 5.52
