Nickdev8/LedScreen/daftpunkfiles/thomas/p1/files/Thomas_Helmet-EarCap.stl

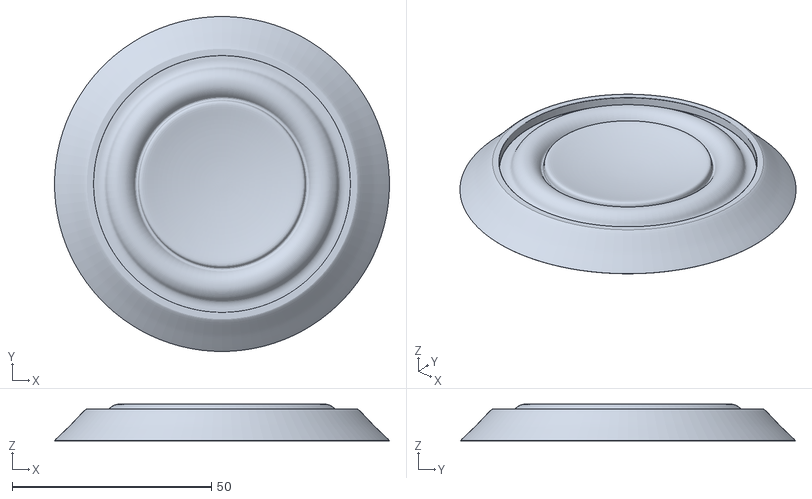
[picture p88: CAD file, 2026-06-18]
daftpunkfiles/thomas/p1/files/Thomas_Helmet-EarCap.stl
84.0 x 84.0 x 9.24
