Nickdev8/LedScreen/daftpunkfiles/visorwithholes3.3mf

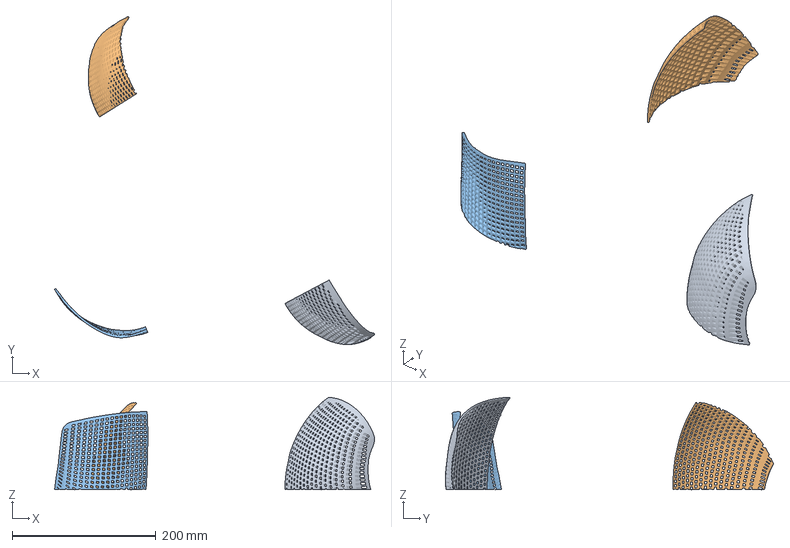
[picture p89: CAD file, 2026-06-18]
daftpunkfiles/visorwithholes3.3mf
445.9 x 457.3 x 128.6 mm
visorwithholes3.stl
visorwithholes2.stl
visorwithholes1.stl
