Nickdev8/LedScreen/daftpunkfiles/guy manual/files/VisorMidBottom-v1.5.stl

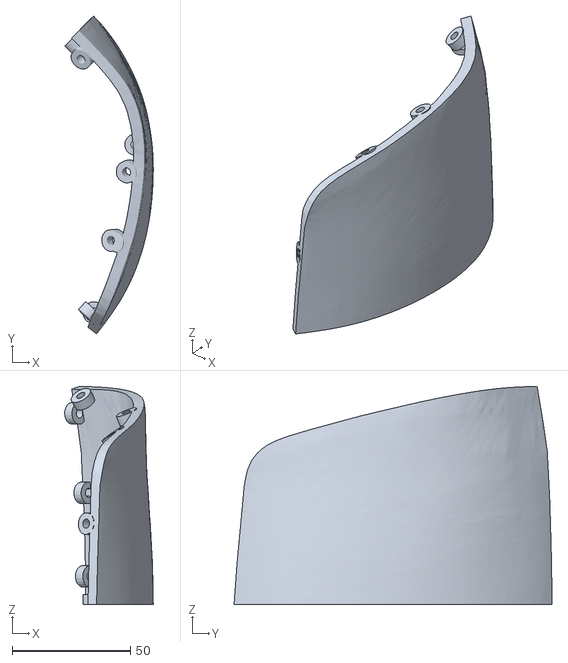
[picture p90: CAD file, 2026-06-18]
daftpunkfiles/guy manual/files/VisorMidBottom-v1.5.stl
37.4 x 134.4 x 92.2
