Nickdev8/LedScreen/daftpunkfiles/thomas/p1/files/Thomas_Helmet-Dome-Side-V1.5.stl

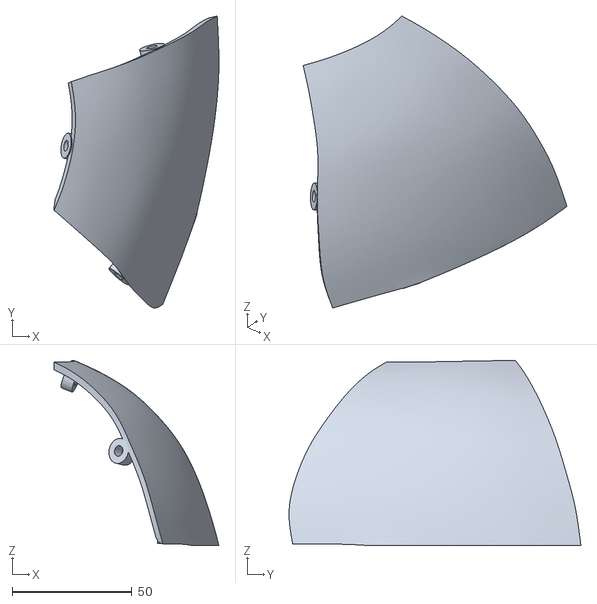
[picture p91: CAD file, 2026-06-18]
daftpunkfiles/thomas/p1/files/Thomas_Helmet-Dome-Side-V1.5.stl
68.9 x 122.0 x 77.3
