Nickdev8/LedScreen/daftpunkfiles/guy manual/files/SideBottom-v1.5.stl

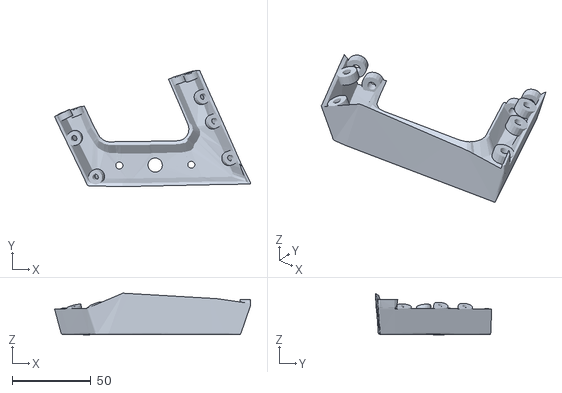
[picture p92: CAD file, 2026-06-18]
daftpunkfiles/guy manual/files/SideBottom-v1.5.stl
124.3 x 73.7 x 26.4
