Nickdev8/LedScreen/daftpunkfiles/thomas/p1/files/Thomas_Helmet-EarMount-v1.5.stl

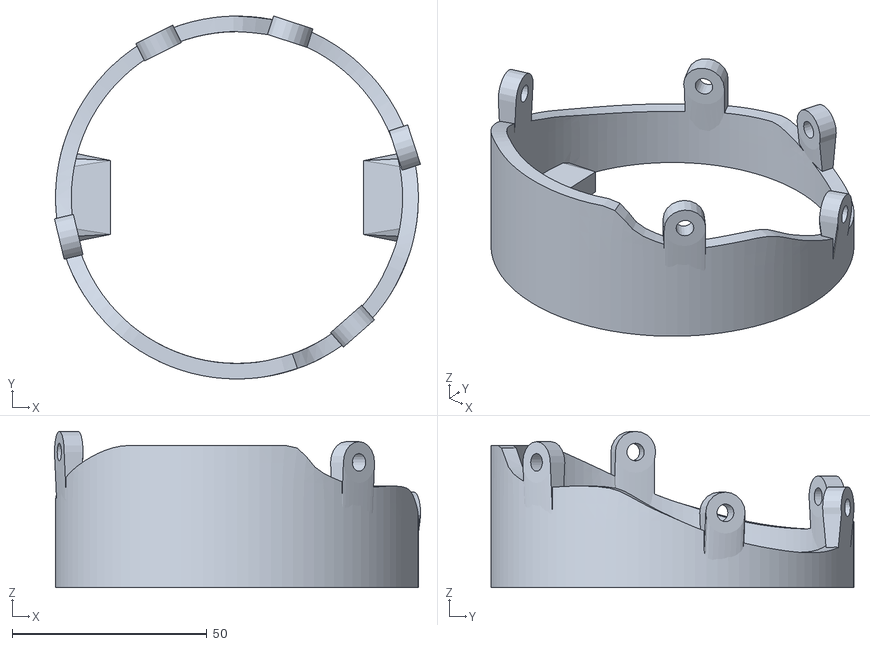
[picture p93: CAD file, 2026-06-18]
daftpunkfiles/thomas/p1/files/Thomas_Helmet-EarMount-v1.5.stl
94.0 x 93.2 x 40.1
