Nickdev8/LedScreen/daftpunkfiles/guy manual/files/TopBar-v1.5.stl

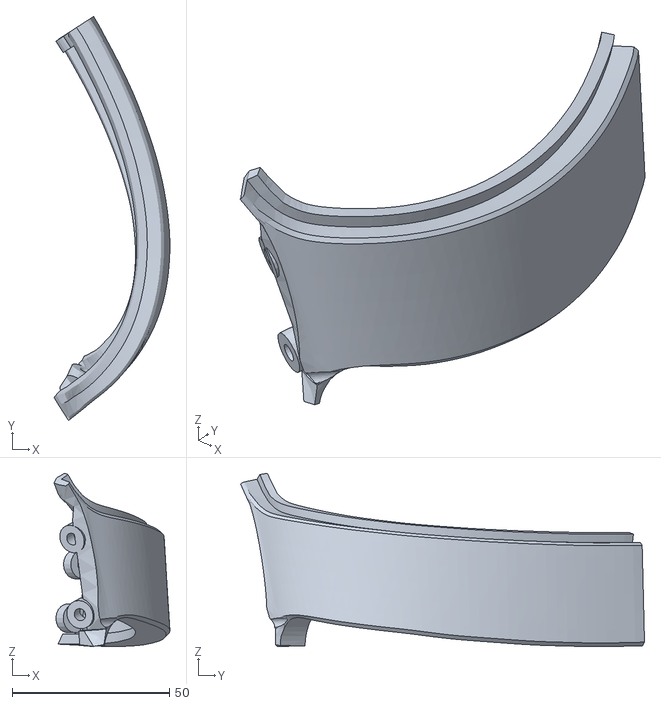
[picture p94: CAD file, 2026-06-18]
daftpunkfiles/guy manual/files/TopBar-v1.5.stl
36.8 x 128.5 x 55.1
