Nickdev8/LedScreen/daftpunkfiles/thomas/p1/files/Thomas_Helmet-Dome-SideTip-V1.5.stl

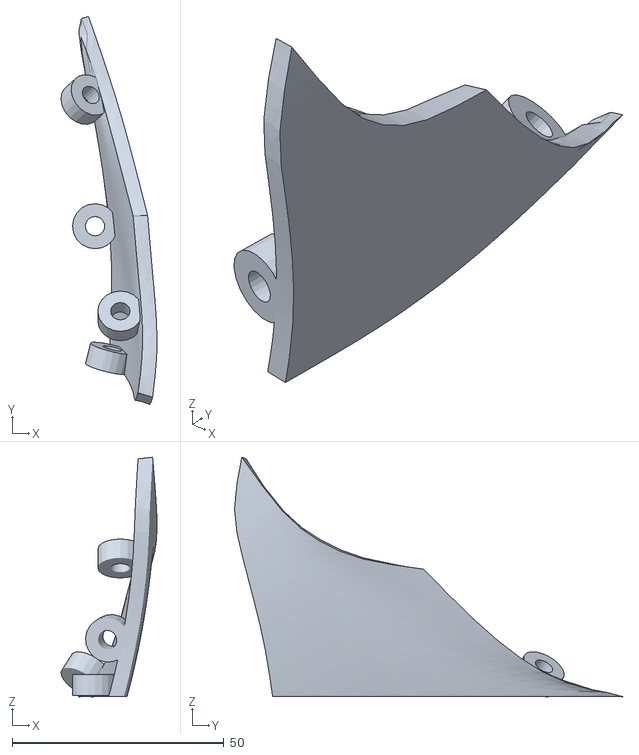
[picture p95: CAD file, 2026-06-18]
daftpunkfiles/thomas/p1/files/Thomas_Helmet-Dome-SideTip-V1.5.stl
22.7 x 91.7 x 56.6
