Nickdev8/LedScreen/daftpunkfiles/guy manual/files/Fan-2L-v1.5.stl

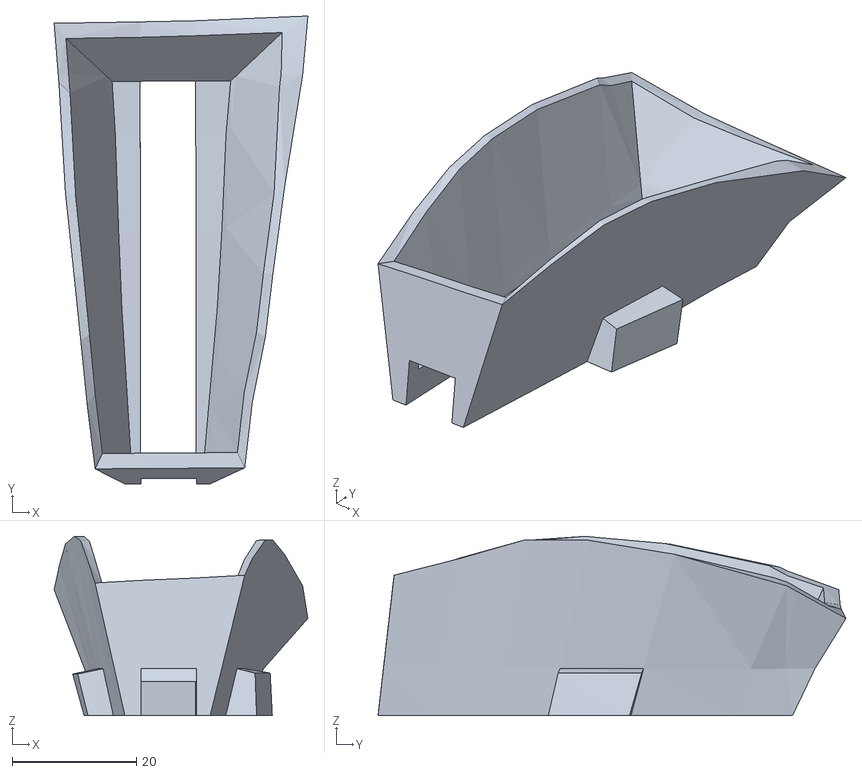
[picture p96: CAD file, 2026-06-18]
daftpunkfiles/guy manual/files/Fan-2L-v1.5.stl
40.9 x 75.5 x 28.9
