Nickdev8/LedScreen/daftpunkfiles/thomas/p1/files/Thomas_Helmet-TopVisor-Side.stl

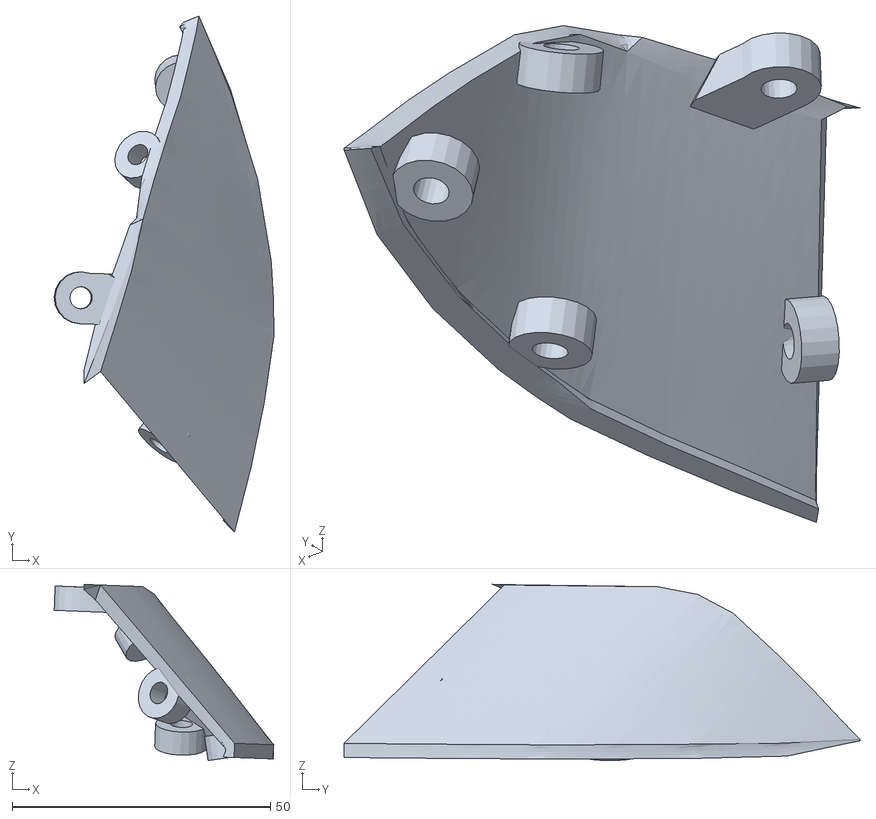
[picture p97: CAD file, 2026-06-18]
daftpunkfiles/thomas/p1/files/Thomas_Helmet-TopVisor-Side.stl
42.5 x 99.9 x 34.1
