Nickdev8/LedScreen/daftpunkfiles/guy manual/files/GuyMan_v2.0mf.3mf

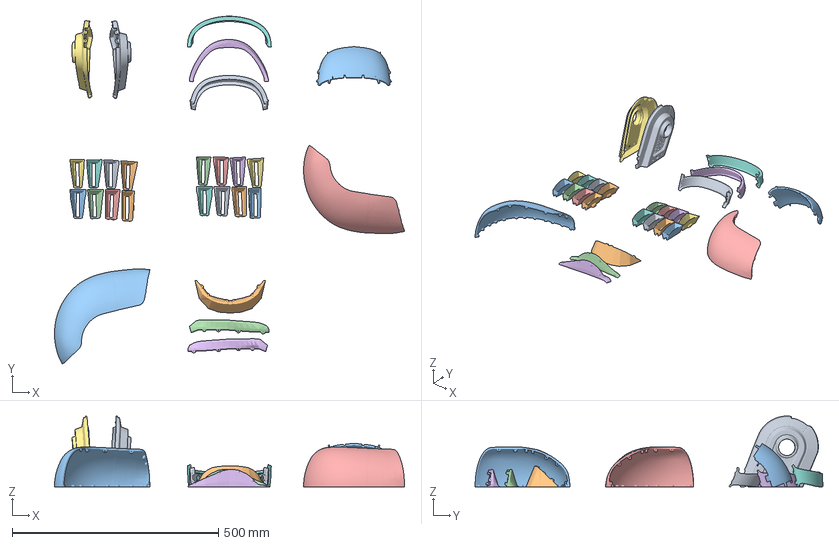
[picture p98: CAD file, 2026-06-18]
daftpunkfiles/guy manual/files/GuyMan_v2.0mf.3mf
847.5 x 842.4 x 171.7 mm
Side-v2.stl x 2
Visor_Buck_Front_v2.0.stl
Visor_Buck_Right_V2.0.stl x 2
Visor_Buck_Side_v2.0.stl x 2
Visor_LEDS-01_v2.0.stl x 2
Visor_LEDS-02_v2.0.stl x 2
Visor_LEDS-03_v2.0.stl x 2
Visor_LEDS-04_v2.0.stl x 2
Visor_LEDS-05_v2.0.stl x 2
Visor_LEDS-06_v2.0.stl x 2
Visor_LEDS-07_v2.0.stl x 2
Chin-v2.stl
Top-v2.stl
Back-v2.stl
Visor_LEDS-08_v2.0.stl x 2
Back_Wires-v2.stl
