Nickdev8/LedScreen/daftpunkfiles/thomas/p1/files/DisplayupperBracket-v1.3.stl

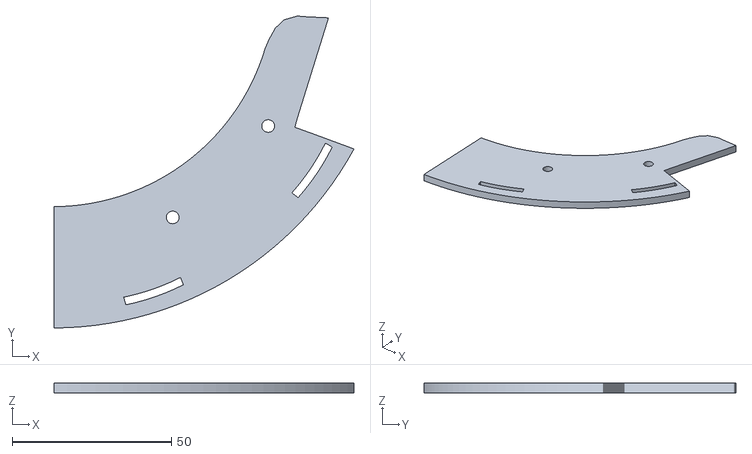
[picture p99: CAD file, 2026-06-18]
daftpunkfiles/thomas/p1/files/DisplayupperBracket-v1.3.stl
94.2 x 97.9 x 3.00
