Nickdev8/LedScreen/daftpunkfiles/guy manual/files/VisorSideVacSupportMid-v1.5.stl

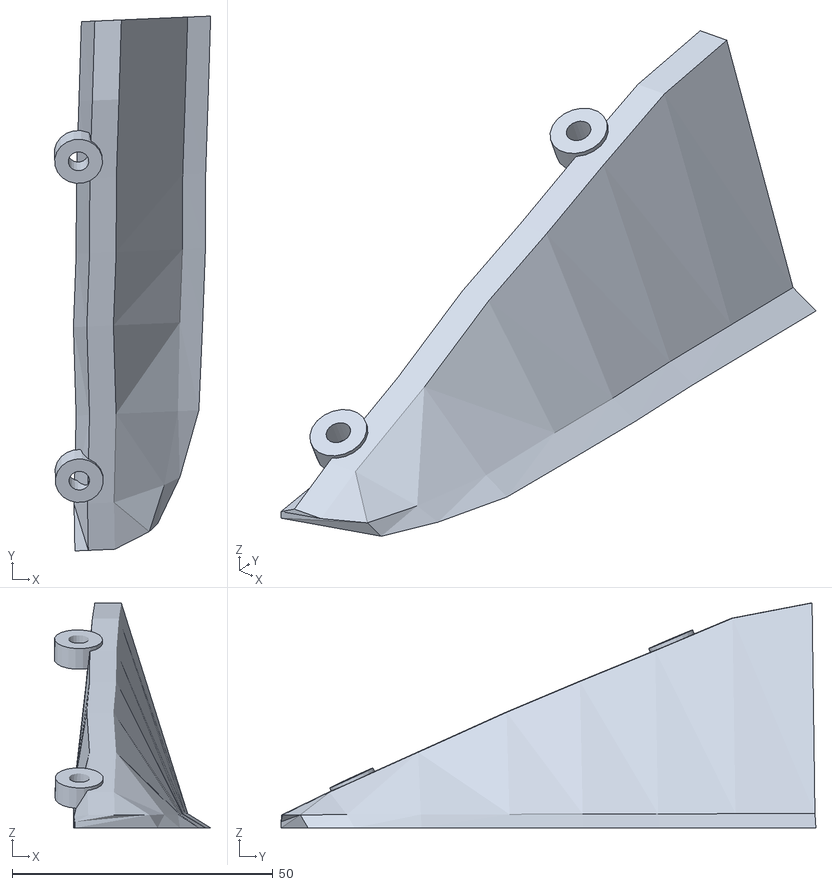
[picture p100: CAD file, 2026-06-18]
daftpunkfiles/guy manual/files/VisorSideVacSupportMid-v1.5.stl
30.0 x 102.5 x 43.1
