Nickdev8/LedScreen/daftpunkfiles/guy manual/files/BackBar-v1.5.stl

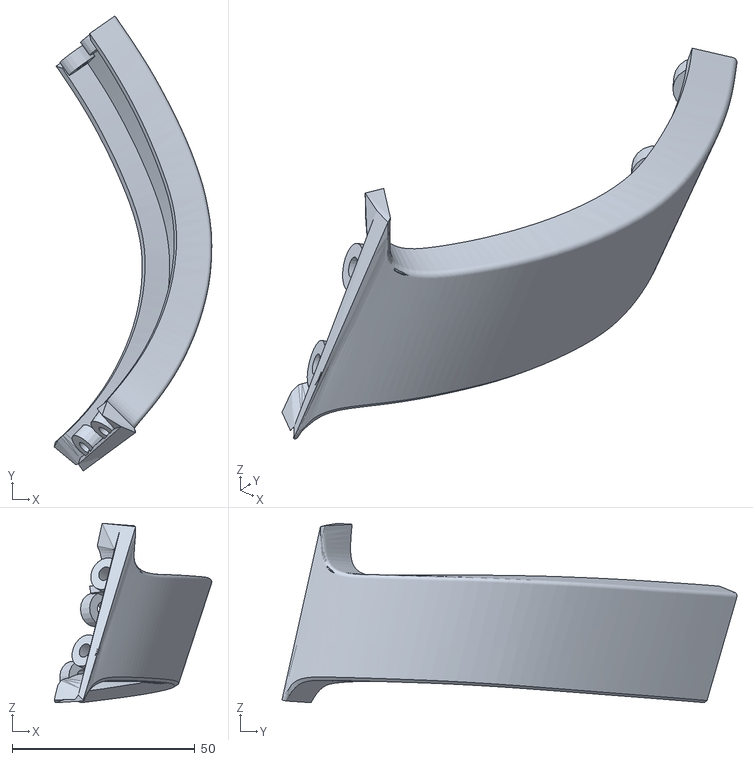
[picture p102: CAD file, 2026-06-18]
daftpunkfiles/guy manual/files/BackBar-v1.5.stl
43.1 x 124.5 x 49.1
