Nickdev8/LedScreen/daftpunkfiles/thomas/p1/files/Thomas_Helmet-Cheek-V1.5.stl

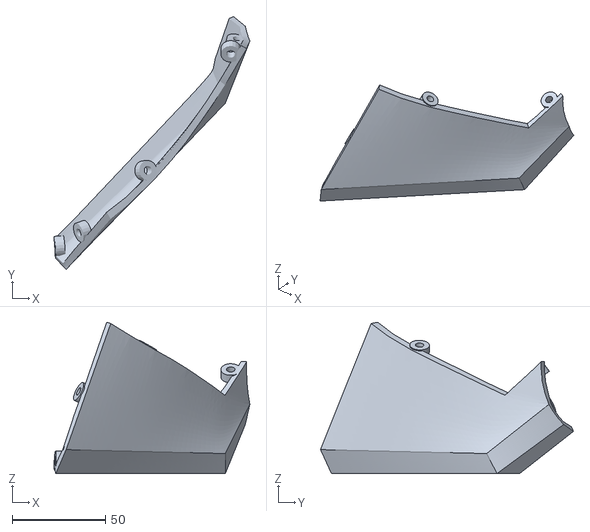
[picture p103: CAD file, 2026-06-18]
daftpunkfiles/thomas/p1/files/Thomas_Helmet-Cheek-V1.5.stl
104.8 x 135.4 x 81.1
