Nickdev8/LedScreen/daftpunkfiles/guy manual/files/Chin-v1.5.stl

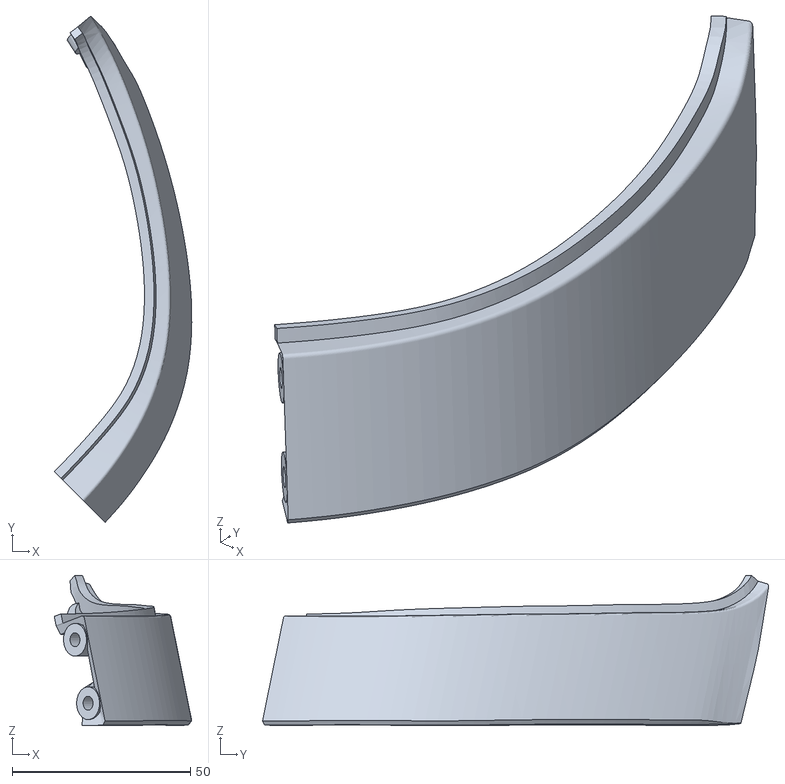
[picture p104: CAD file, 2026-06-18]
daftpunkfiles/guy manual/files/Chin-v1.5.stl
38.6 x 142.0 x 42.2
