Nickdev8/LedScreen/daftpunkfiles/thomas/p1/files/DisplayLowerBracket-v1.3.stl

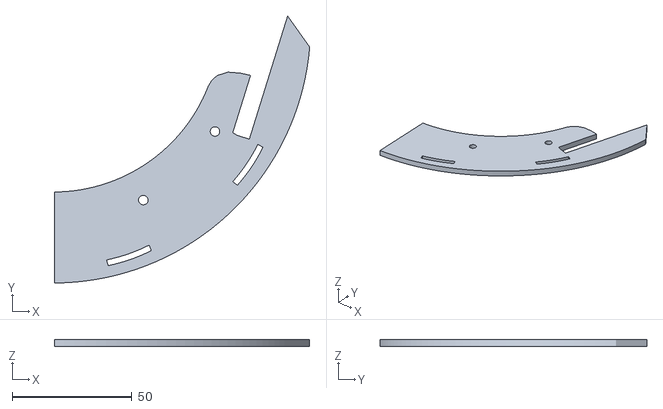
[picture p105: CAD file, 2026-06-18]
daftpunkfiles/thomas/p1/files/DisplayLowerBracket-v1.3.stl
106.9 x 111.7 x 3.00
