Nickdev8/LedScreen/daftpunkfiles/guy manual/files/VisorBottom-v1.5.stl

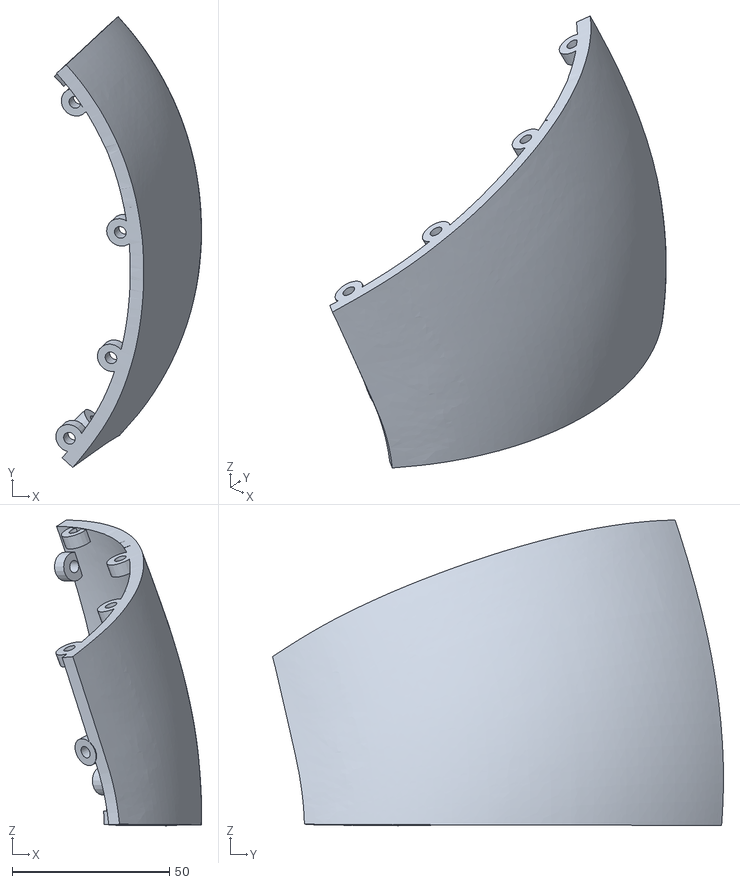
[picture p106: CAD file, 2026-06-18]
daftpunkfiles/guy manual/files/VisorBottom-v1.5.stl
46.8 x 143.4 x 97.2
