Nickdev8/LedScreen/daftpunkfiles/thomas/p1/files/Thomas_Helmet-Visor-TopFront.stl

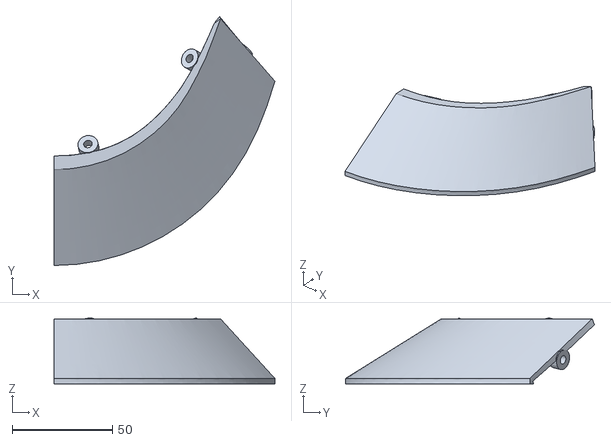
[picture p107: CAD file, 2026-06-18]
daftpunkfiles/thomas/p1/files/Thomas_Helmet-Visor-TopFront.stl
109.9 x 123.9 x 32.8
