Nickdev8/LedScreen/daftpunkfiles/guy manual/files/EarCupLR-Electronics-V1.5.stl

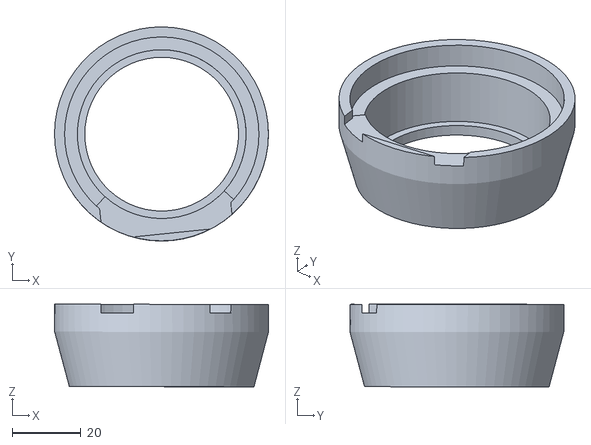
[picture p108: CAD file, 2026-06-18]
daftpunkfiles/guy manual/files/EarCupLR-Electronics-V1.5.stl
62.0 x 62.1 x 24.0
