Nickdev8/LedScreen/daftpunkfiles/thomas/p1/files/Thomas_Helmet-Mouth.stl

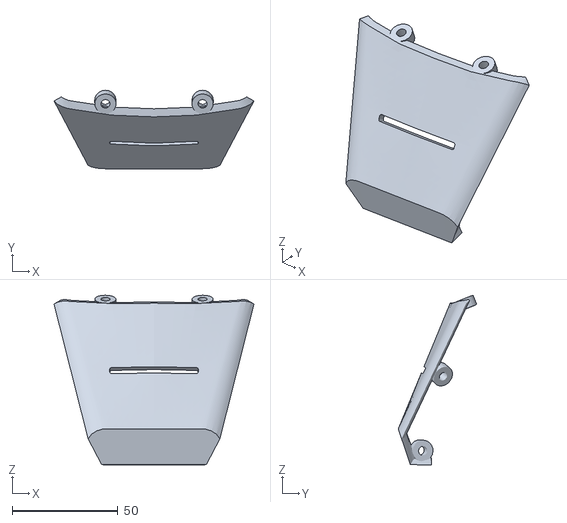
[picture p109: CAD file, 2026-06-18]
daftpunkfiles/thomas/p1/files/Thomas_Helmet-Mouth.stl
94.4 x 37.1 x 80.1
