Nickdev8/LedScreen/daftpunkfiles/guy manual/files/SideShroud-BB-v1.5.stl

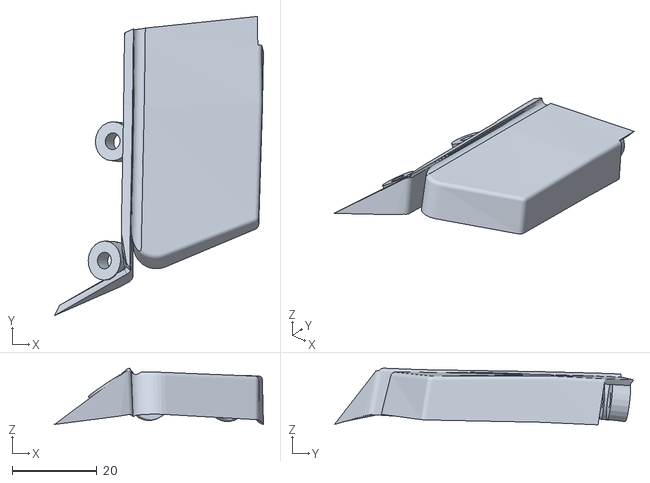
[picture p110: CAD file, 2026-06-18]
daftpunkfiles/guy manual/files/SideShroud-BB-v1.5.stl
49.2 x 70.4 x 13.4
