Nickdev8/LedScreen/daftpunkfiles/thomas/p1/files/Thomas_Helmet-Visor-Side-V1.5.stl

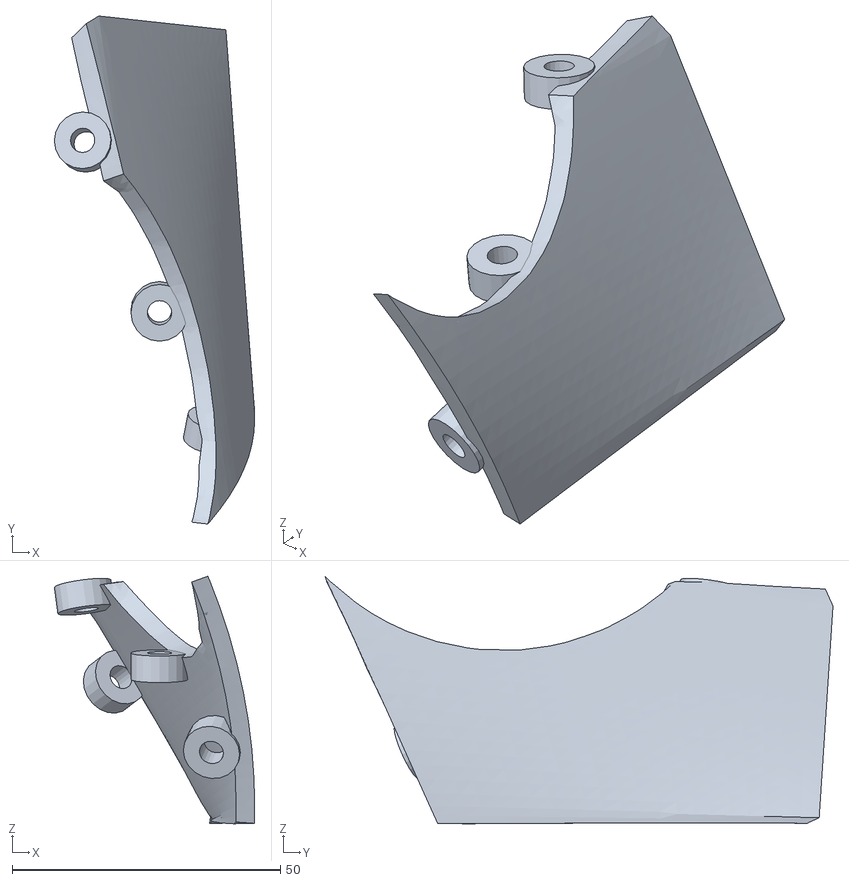
[picture p111: CAD file, 2026-06-18]
daftpunkfiles/thomas/p1/files/Thomas_Helmet-Visor-Side-V1.5.stl
37.3 x 94.7 x 46.2
