Nickdev8/LedScreen/daftpunkfiles/guy manual/files/VisorTop-v1.5.stl

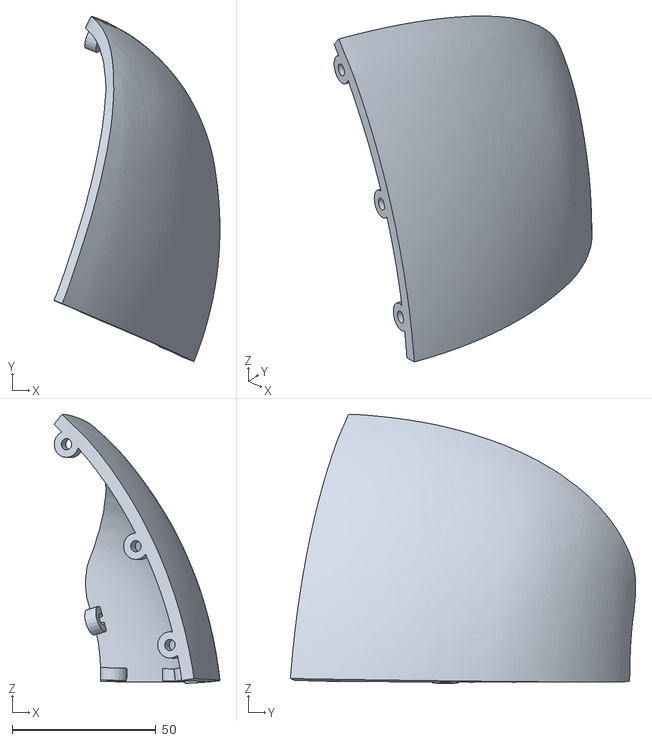
[picture p112: CAD file, 2026-06-18]
daftpunkfiles/guy manual/files/VisorTop-v1.5.stl
57.8 x 120.2 x 93.7
