Nickdev8/LedScreen/daftpunkfiles/thomas/p1/files/Thomas_Helmet-TopVisor-Side-V1.5.stl

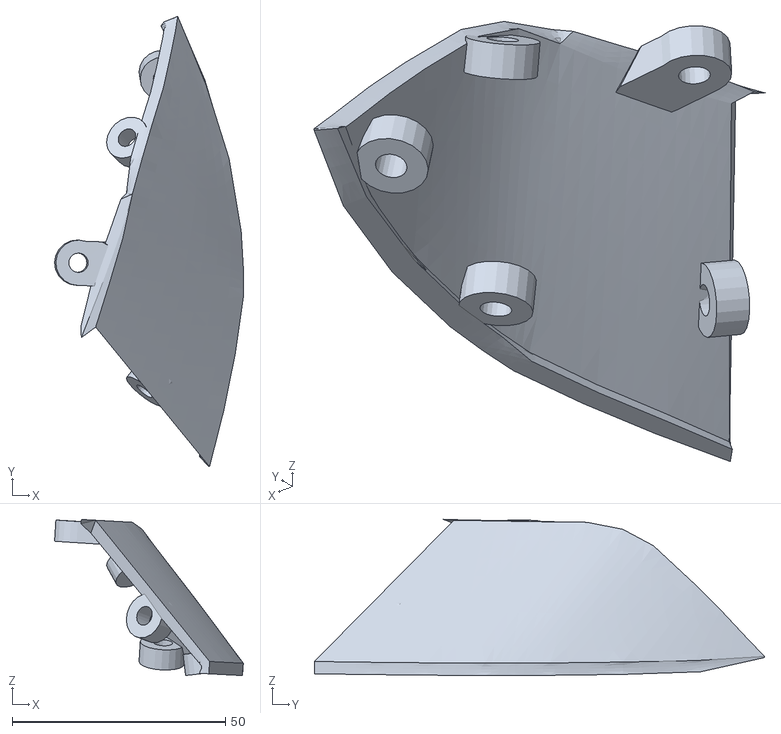
[picture p113: CAD file, 2026-06-18]
daftpunkfiles/thomas/p1/files/Thomas_Helmet-TopVisor-Side-V1.5.stl
44.4 x 105.7 x 36.6
