Nickdev8/LedScreen/daftpunkfiles/guy manual/files/EarCupElectronicsBracket-V1.5.stl

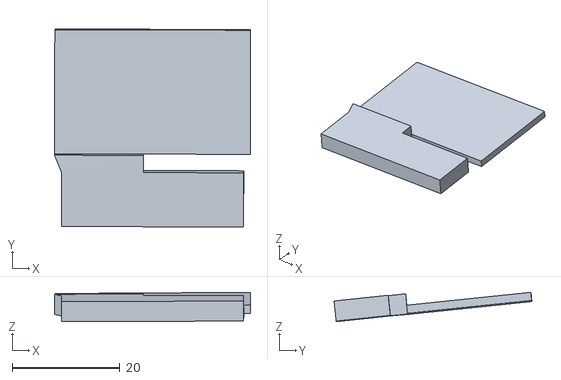
[picture p114: CAD file, 2026-06-18]
daftpunkfiles/guy manual/files/EarCupElectronicsBracket-V1.5.stl
36.3 x 36.7 x 5.44
