Nickdev8/LedScreen/daftpunkfiles/guy manual/files/Fan-3L-v1.5.stl

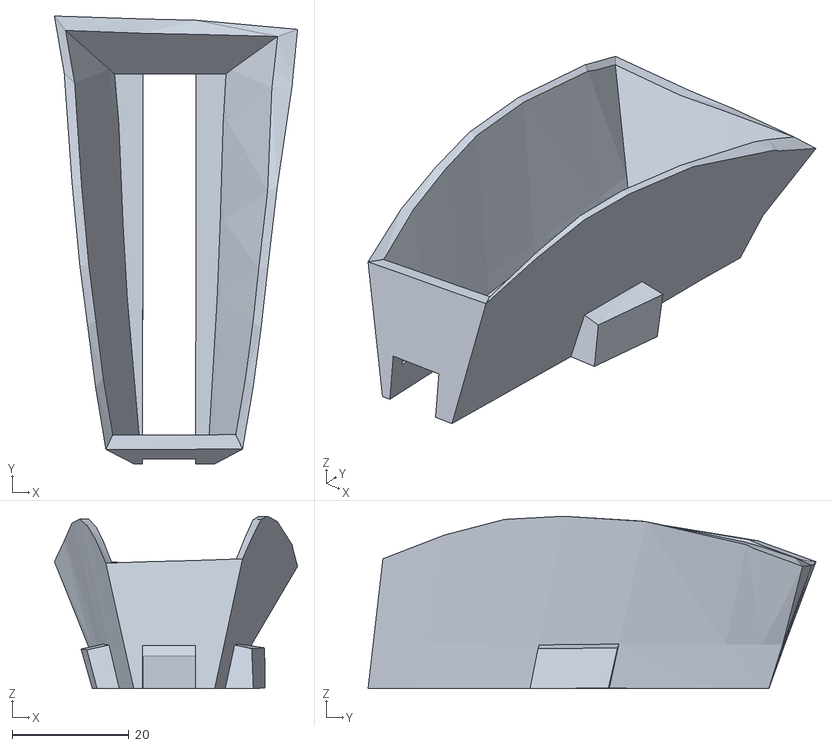
[picture p116: CAD file, 2026-06-18]
daftpunkfiles/guy manual/files/Fan-3L-v1.5.stl
41.7 x 76.8 x 29.6
