Nickdev8/LedScreen/daftpunkfiles/thomas/p1/files/LightRing-v1.0.stl

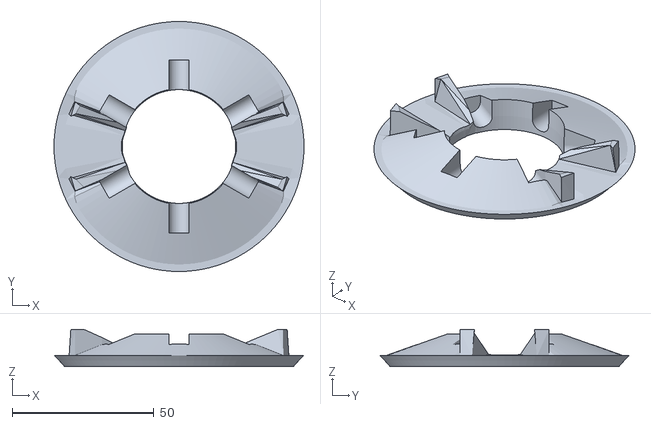
[picture p117: CAD file, 2026-06-18]
daftpunkfiles/thomas/p1/files/LightRing-v1.0.stl
88.1 x 88.1 x 13.1
