Nickdev8/LedScreen/daftpunkfiles/guy manual/files/SideShroud-TB-v1.5.stl

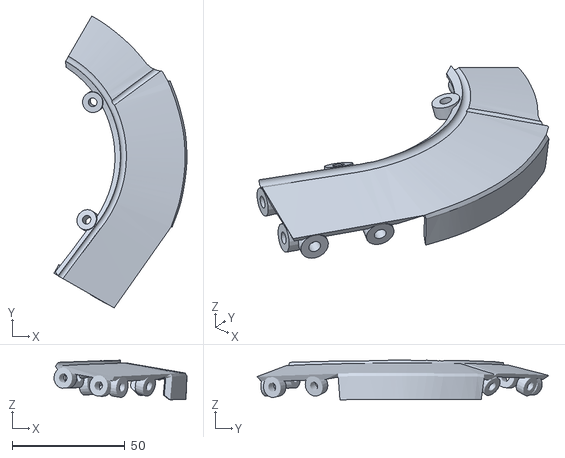
[picture p118: CAD file, 2026-06-18]
daftpunkfiles/guy manual/files/SideShroud-TB-v1.5.stl
59.0 x 129.4 x 17.6
