Nickdev8/LedScreen/daftpunkfiles/thomas/p1/files/Thomas_Helmet-Cheek.stl

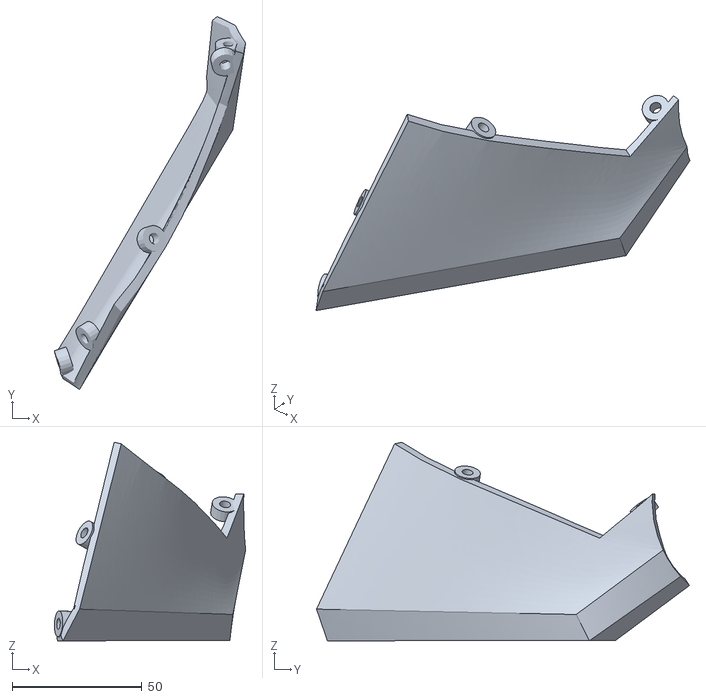
[picture p119: CAD file, 2026-06-18]
daftpunkfiles/thomas/p1/files/Thomas_Helmet-Cheek.stl
73.8 x 144.0 x 76.6
