Nickdev8/LedScreen/daftpunkfiles/guy manual/files/Fan-7L-v1.5.stl

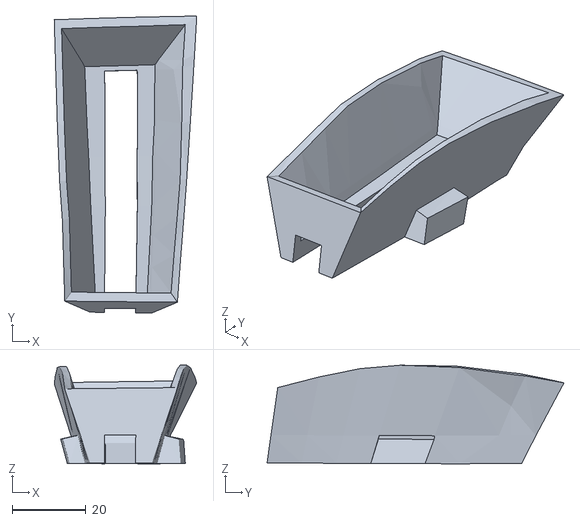
[picture p120: CAD file, 2026-06-18]
daftpunkfiles/guy manual/files/Fan-7L-v1.5.stl
38.6 x 80.5 x 26.8
