Nickdev8/LedScreen/daftpunkfiles/thomas/p1/files/Thomas_Helmet-VisorL.stl

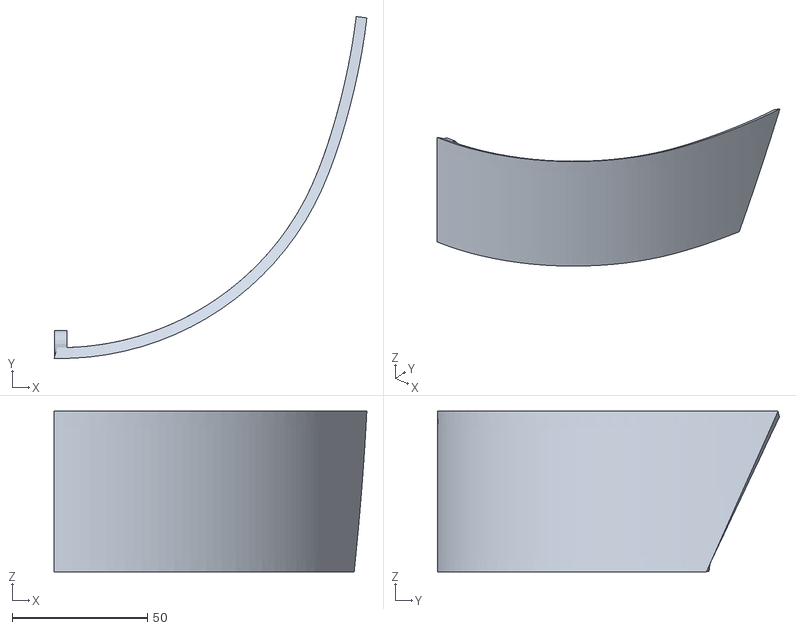
[picture p121: CAD file, 2026-06-18]
daftpunkfiles/thomas/p1/files/Thomas_Helmet-VisorL.stl
115.8 x 126.6 x 59.4
