Nickdev8/LedScreen/daftpunkfiles/guy manual/files/SideTop-v1.5.stl

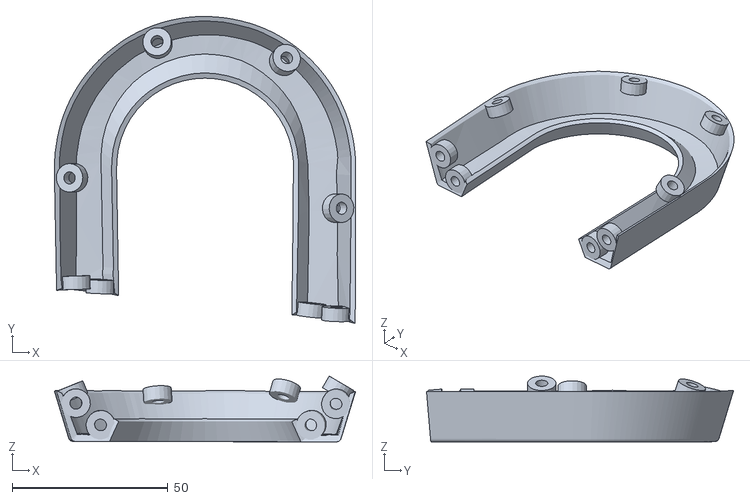
[picture p122: CAD file, 2026-06-18]
daftpunkfiles/guy manual/files/SideTop-v1.5.stl
96.9 x 98.7 x 21.2
