Nickdev8/LedScreen/daftpunkfiles/guy manual/files/SideShroud-BF-v1.5.stl

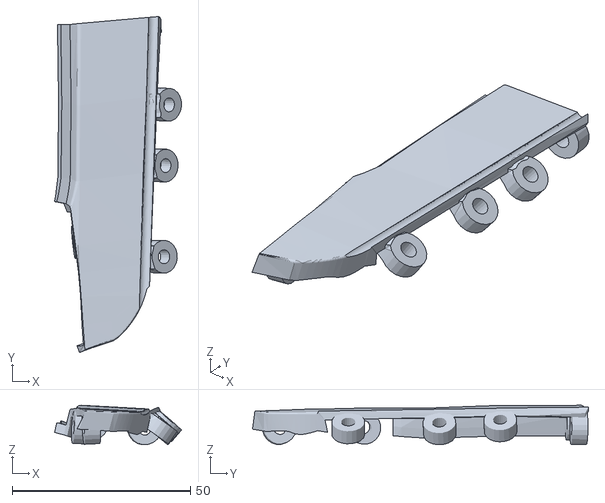
[picture p124: CAD file, 2026-06-18]
daftpunkfiles/guy manual/files/SideShroud-BF-v1.5.stl
35.6 x 94.2 x 11.1
