Nickdev8/LedScreen/daftpunkfiles/thomas/p1/files/Thomas_Helmet-BottomVisor-Front.stl

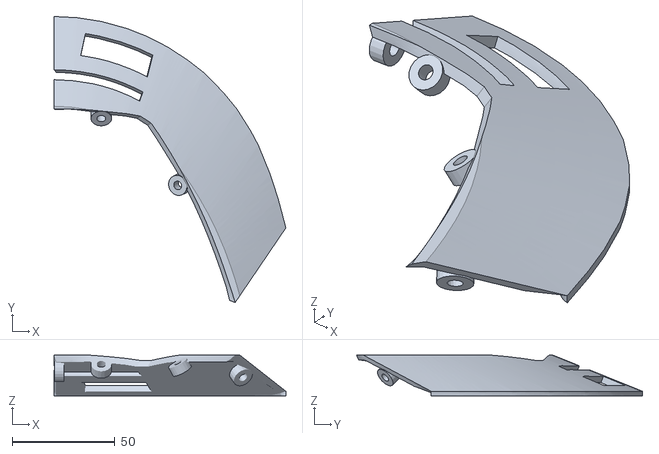
[picture p125: CAD file, 2026-06-18]
daftpunkfiles/thomas/p1/files/Thomas_Helmet-BottomVisor-Front.stl
112.6 x 139.0 x 19.9
