Nickdev8/LedScreen/daftpunkfiles/guy manual/files/Fan-8-BottomL-v1.5.stl

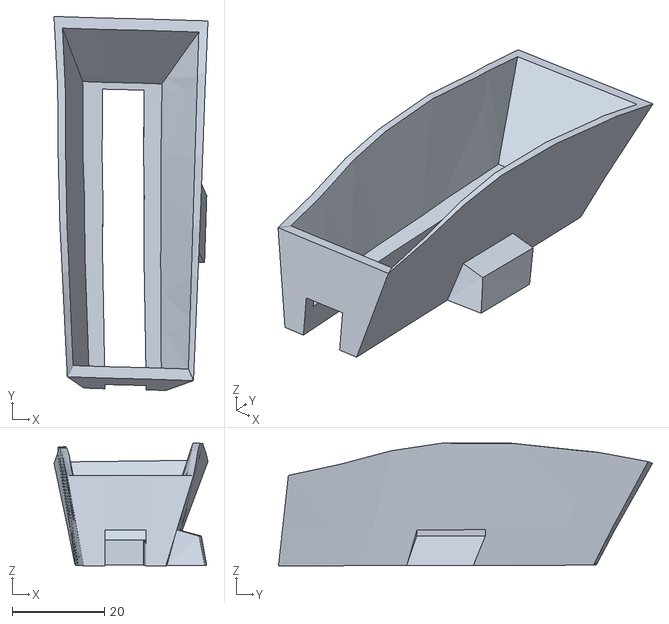
[picture p126: CAD file, 2026-06-18]
daftpunkfiles/guy manual/files/Fan-8-BottomL-v1.5.stl
33.4 x 81.0 x 26.6
