Nickdev8/LedScreen/daftpunkfiles/guy manual/files/VisorSideVacSupportFront-v1.5.stl

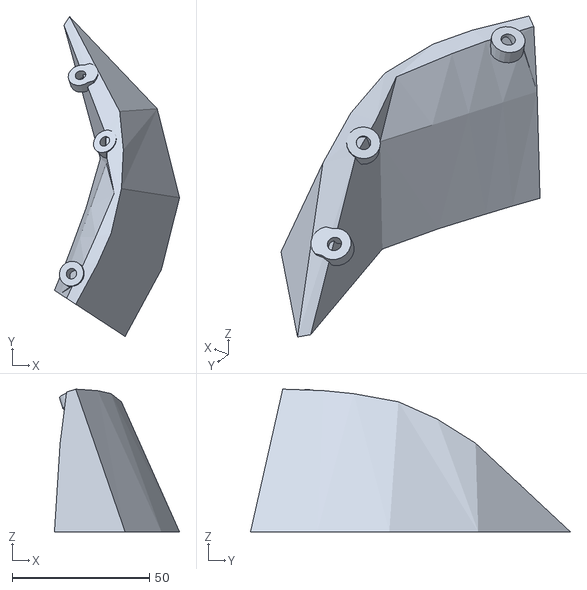
[picture p128: CAD file, 2026-06-18]
daftpunkfiles/guy manual/files/VisorSideVacSupportFront-v1.5.stl
45.6 x 116.6 x 52.0
