Nickdev8/LedScreen/daftpunkfiles/thomas/p1/files/Thomas_Helmet-Dome-Back-Top-V1.5.stl

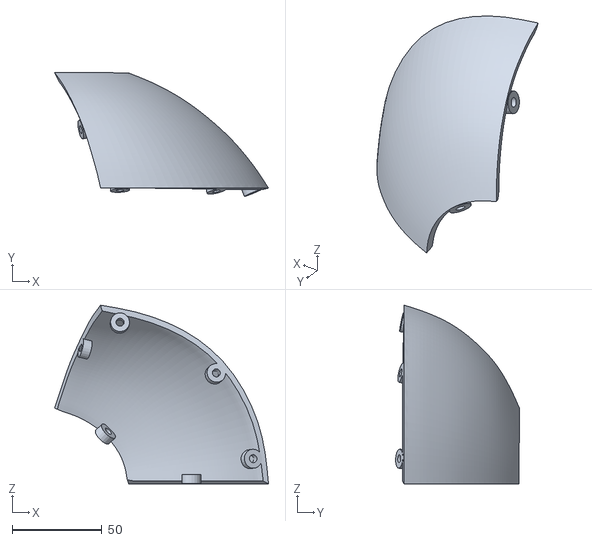
[picture p129: CAD file, 2026-06-18]
daftpunkfiles/thomas/p1/files/Thomas_Helmet-Dome-Back-Top-V1.5.stl
119.5 x 69.1 x 99.8
