Nickdev8/LedScreen/daftpunkfiles/guy manual/files/SideShroud-TF-v1.5.stl

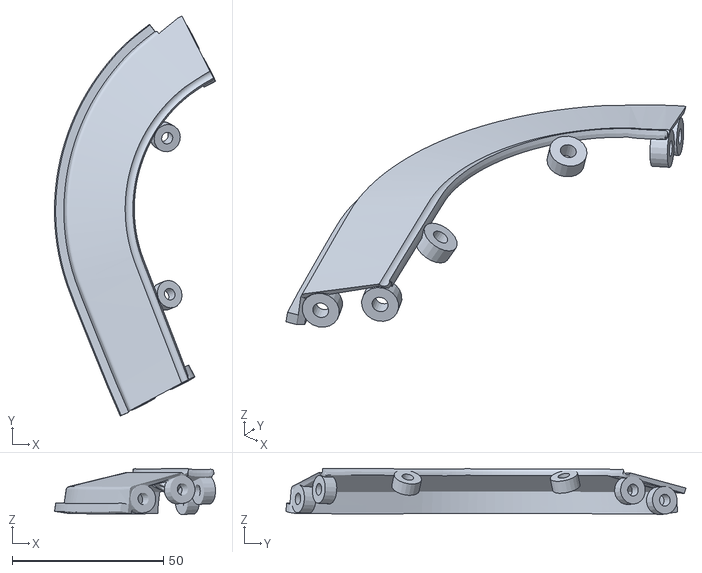
[picture p130: CAD file, 2026-06-18]
daftpunkfiles/guy manual/files/SideShroud-TF-v1.5.stl
53.2 x 132.1 x 15.2
