Nickdev8/LedScreen/daftpunkfiles/guy manual/files/Fan-6L-v1.5.stl

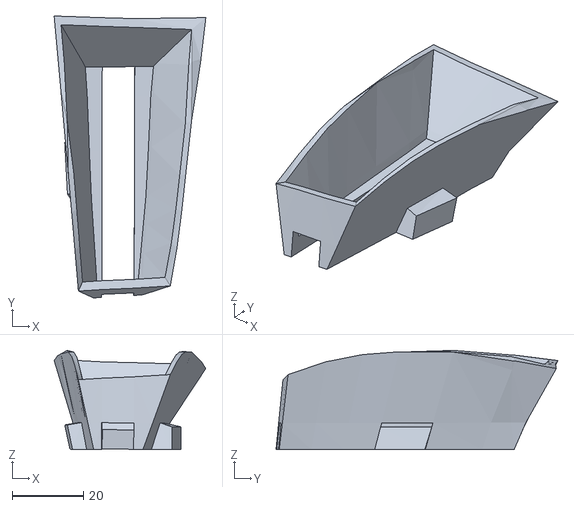
[picture p131: CAD file, 2026-06-18]
daftpunkfiles/guy manual/files/Fan-6L-v1.5.stl
42.6 x 79.1 x 27.8
