Nickdev8/LedScreen/daftpunkfiles/guy manual/files/Fan-5L-v1.5.stl

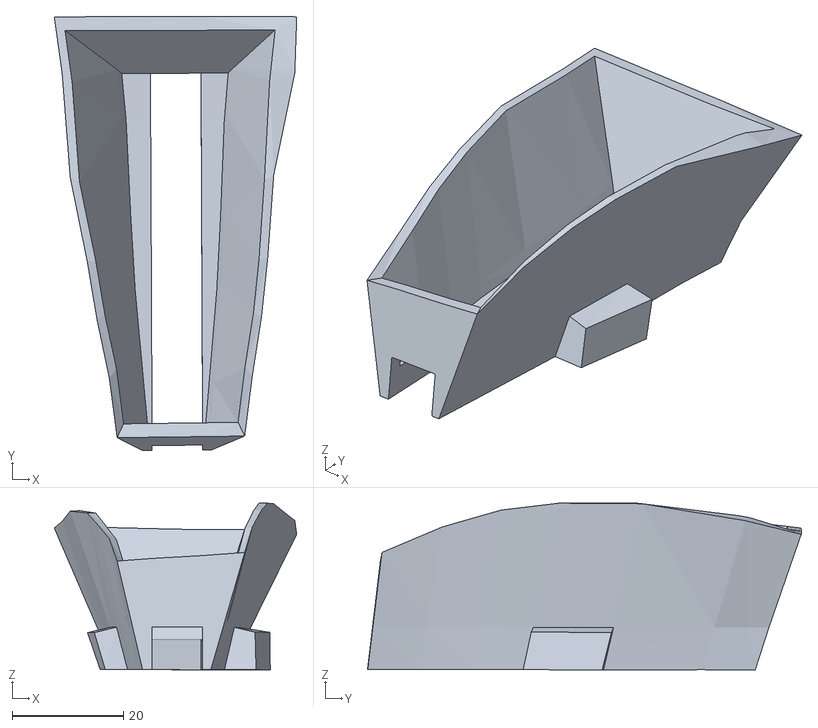
[picture p133: CAD file, 2026-06-18]
daftpunkfiles/guy manual/files/Fan-5L-v1.5.stl
43.6 x 78.0 x 29.9
