Nickdev8/LedScreen/daftpunkfiles/thomas/p1/files/Thomas_Helmet-Visor-TopFront-V1.5.stl

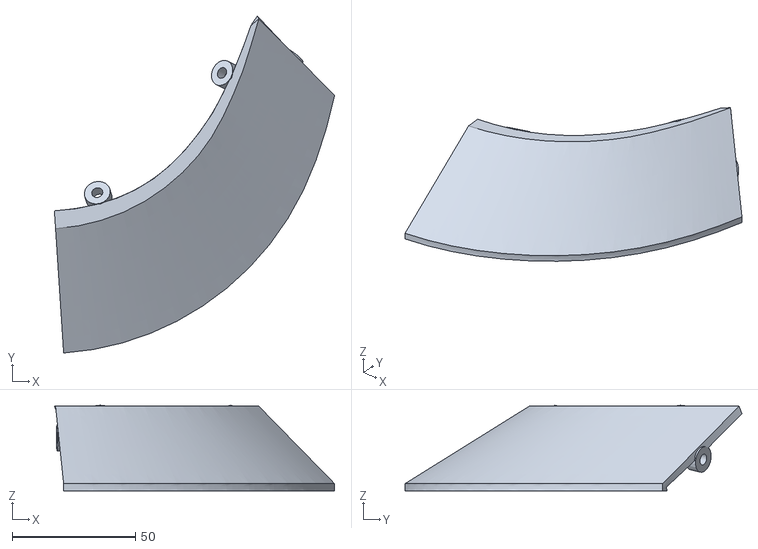
[picture p134: CAD file, 2026-06-18]
daftpunkfiles/thomas/p1/files/Thomas_Helmet-Visor-TopFront-V1.5.stl
113.5 x 136.5 x 34.7
