Nickdev8/LedScreen/daftpunkfiles/guy manual/images/August_06__2014_at_1015PM.jpg

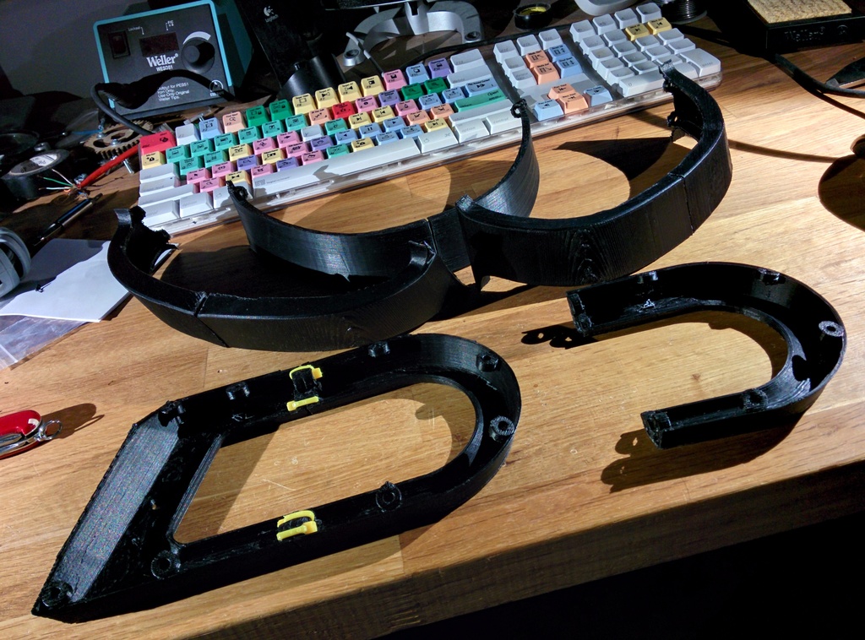
daftpunkfiles/guy manual/images/August_06__2014_at_1015PM.jpg
