Nickdev8/LedScreen/daftpunkfiles/guy manual/images/August_13__2014_at_0832AM.jpg

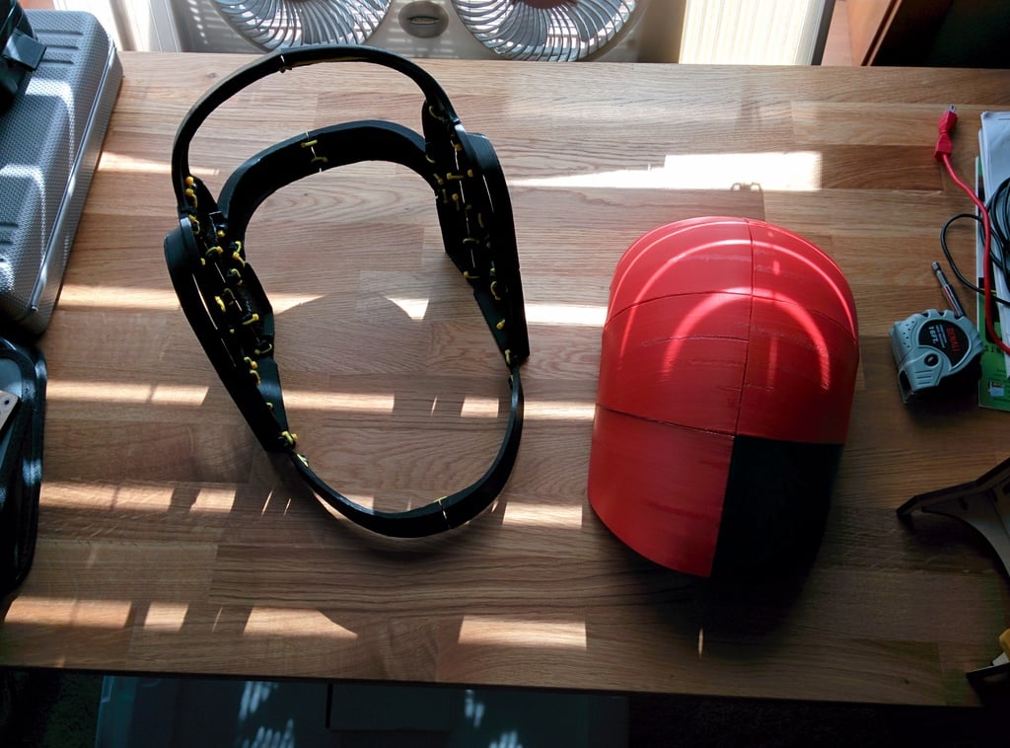
daftpunkfiles/guy manual/images/August_13__2014_at_0832AM.jpg
