Nickdev8/LedScreen/daftpunkfiles/guy manual/images/Screenshot_2025-03-29_161154.png

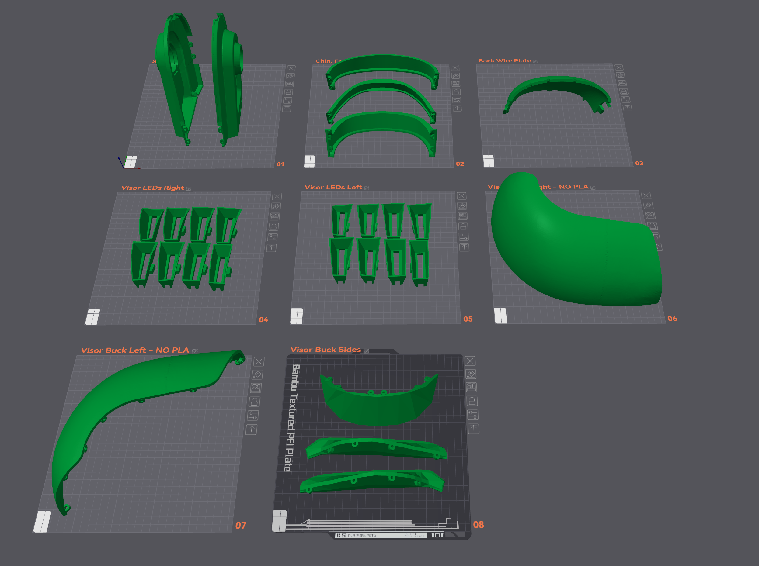
daftpunkfiles/guy manual/images/Screenshot_2025-03-29_161154.png
