Nickdev8/LedScreen/daftpunkfiles/guy manual/images/September_17__2014_at_1122PM.jpg

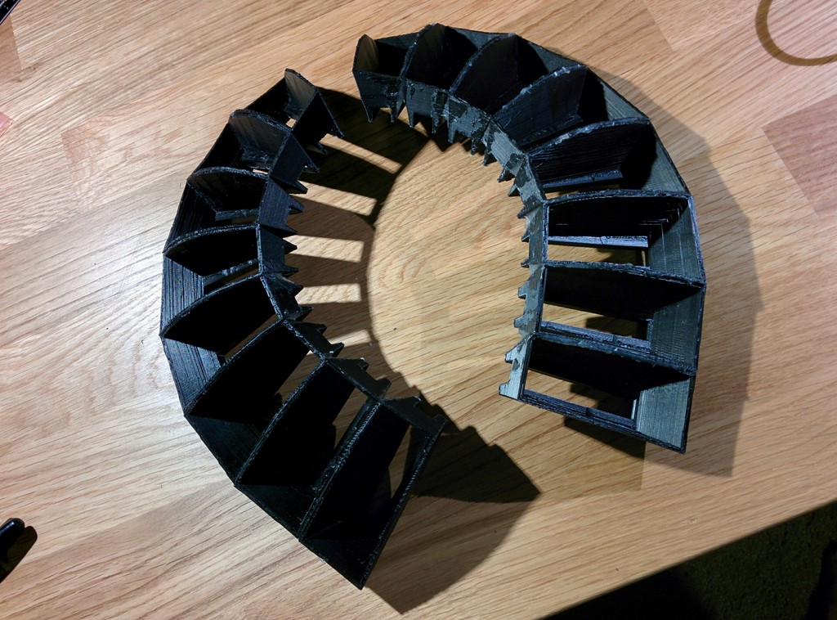
daftpunkfiles/guy manual/images/September_17__2014_at_1122PM.jpg
