Nickdev8/LedScreen/daftpunkfiles/guy manual/images/September_24__2014_at_0923PM.jpg

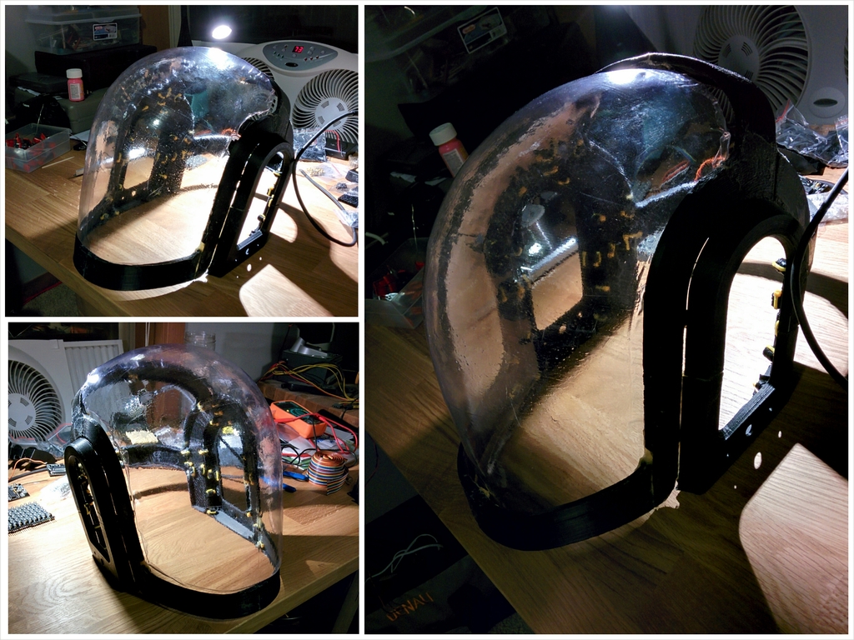
daftpunkfiles/guy manual/images/September_24__2014_at_0923PM.jpg
